alekssandr89/Dixom-m/Dixom_pm/assets/images/jpg/night.jpg

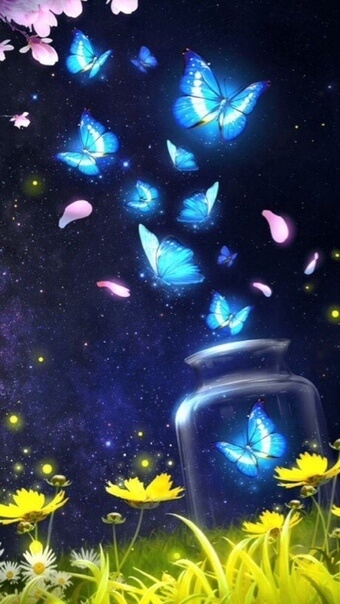
Dixom_pm/assets/images/jpg/night.jpg
