alekssandr89/Dixom-m/Dixom_pm/assets/images/jpg/rotate.jpg

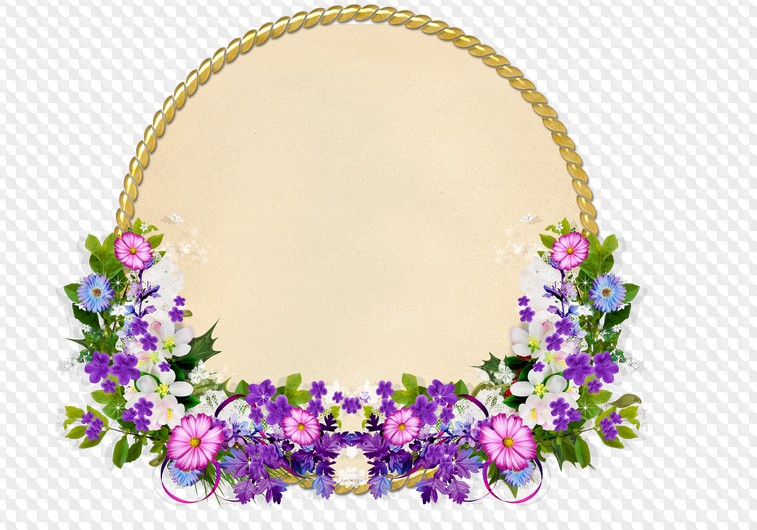
Dixom_pm/assets/images/jpg/rotate.jpg
