alekssandr89/Dixom-m/Dixom_pm/assets/images/png/speaker.png

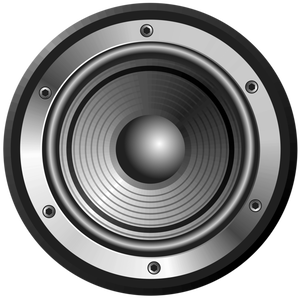
Dixom_pm/assets/images/png/speaker.png
