alekssandr89/Dixom-m/Dixom_pm/assets/texture/noise.jpg

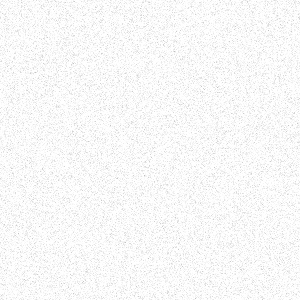
Dixom_pm/assets/texture/noise.jpg
