alekssandr89/Dixom-m/pcb/Base/electrical_diagram.png

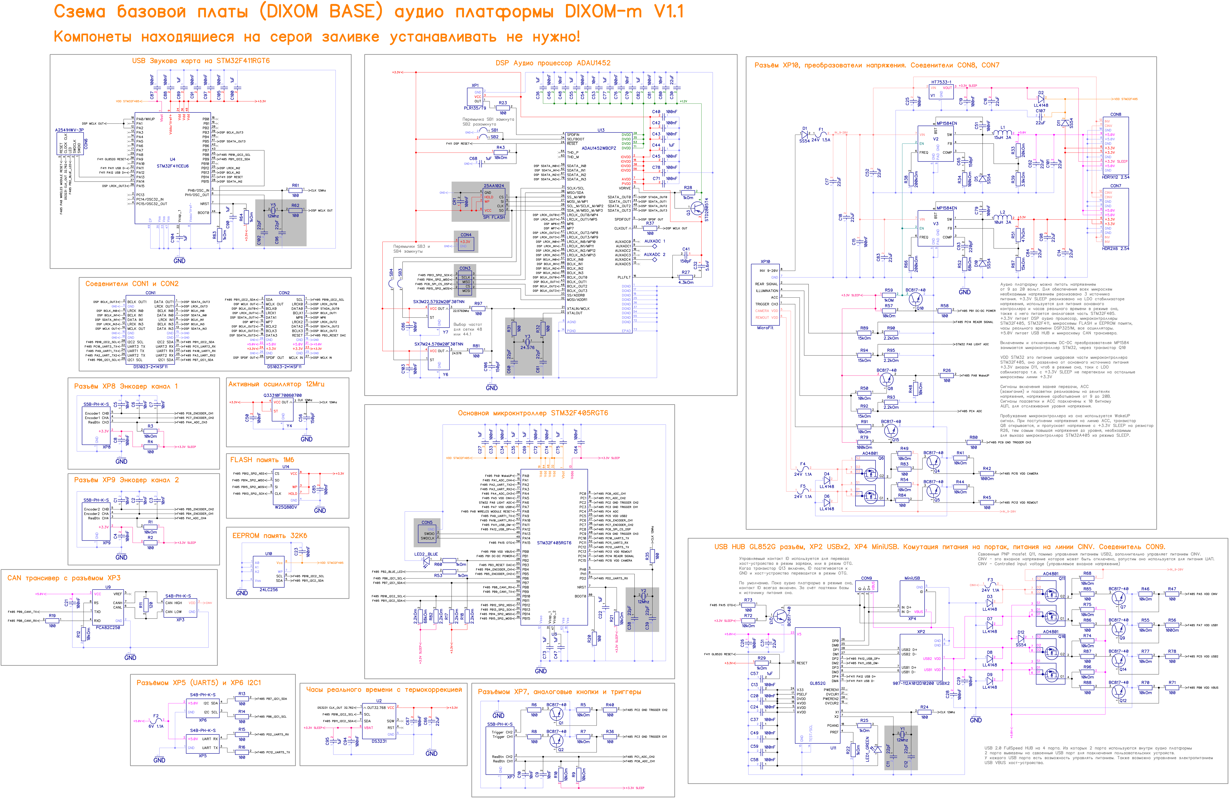
pcb/Base/electrical_diagram.png
