alekssandr89/Dixom-m/pcb/Base/images/1_PCB_TOP.png

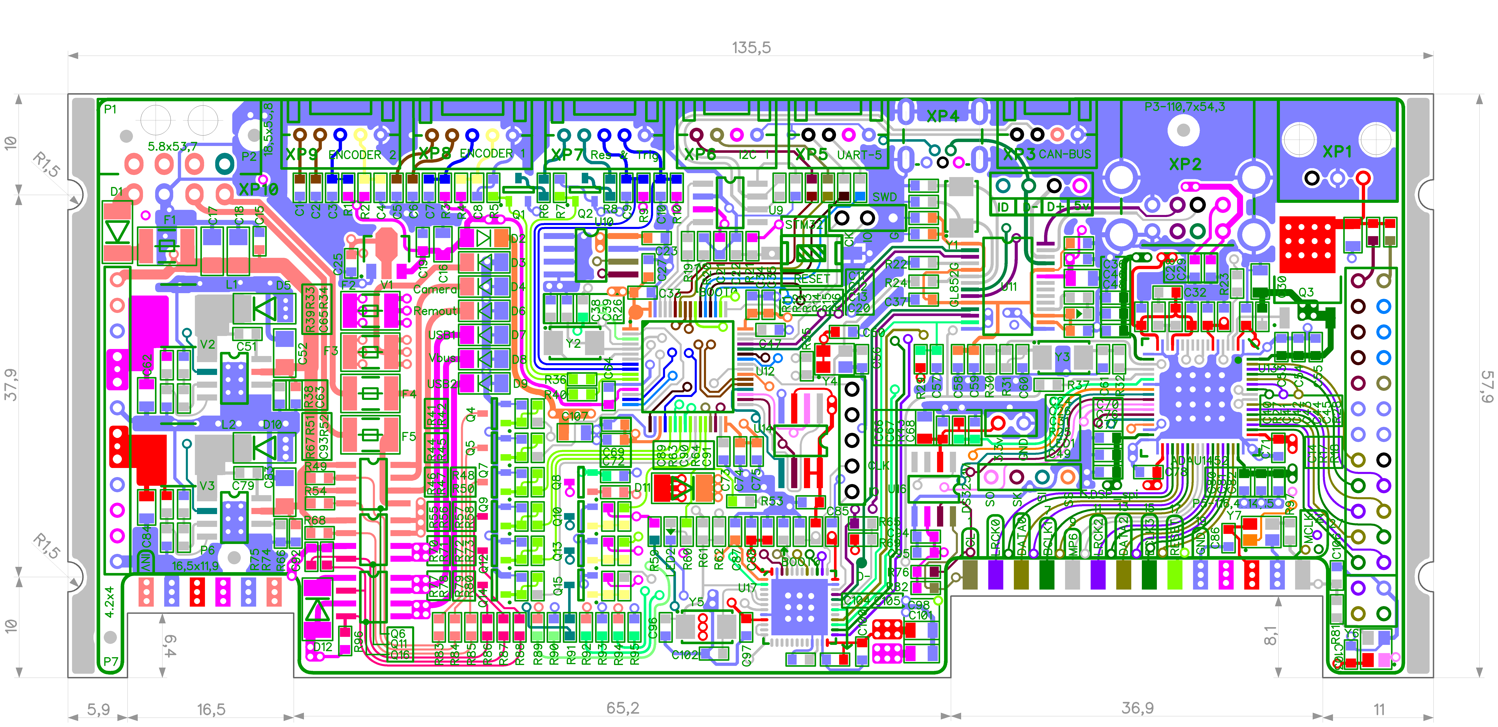
pcb/Base/images/1_PCB_TOP.png
