alekssandr89/Dixom-m/pcb/Base/images/2_PCB_IN1_GND.png

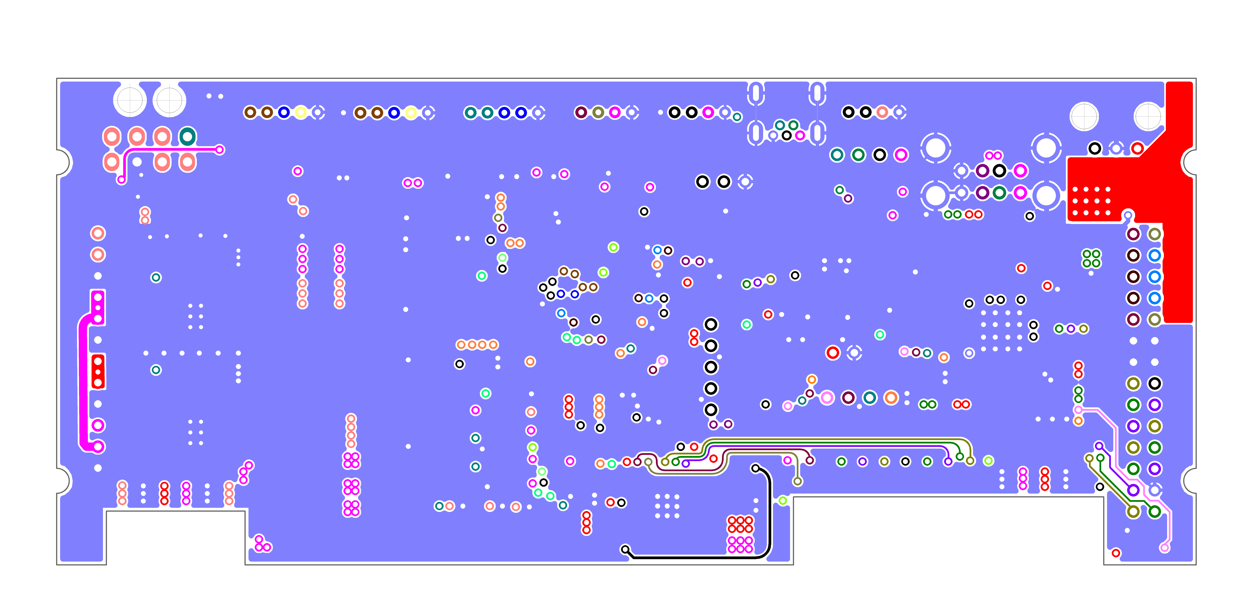
pcb/Base/images/2_PCB_IN1_GND.png
