alekssandr89/Dixom-m/pcb/Base/images/3_PCB_IN2_VCC.png

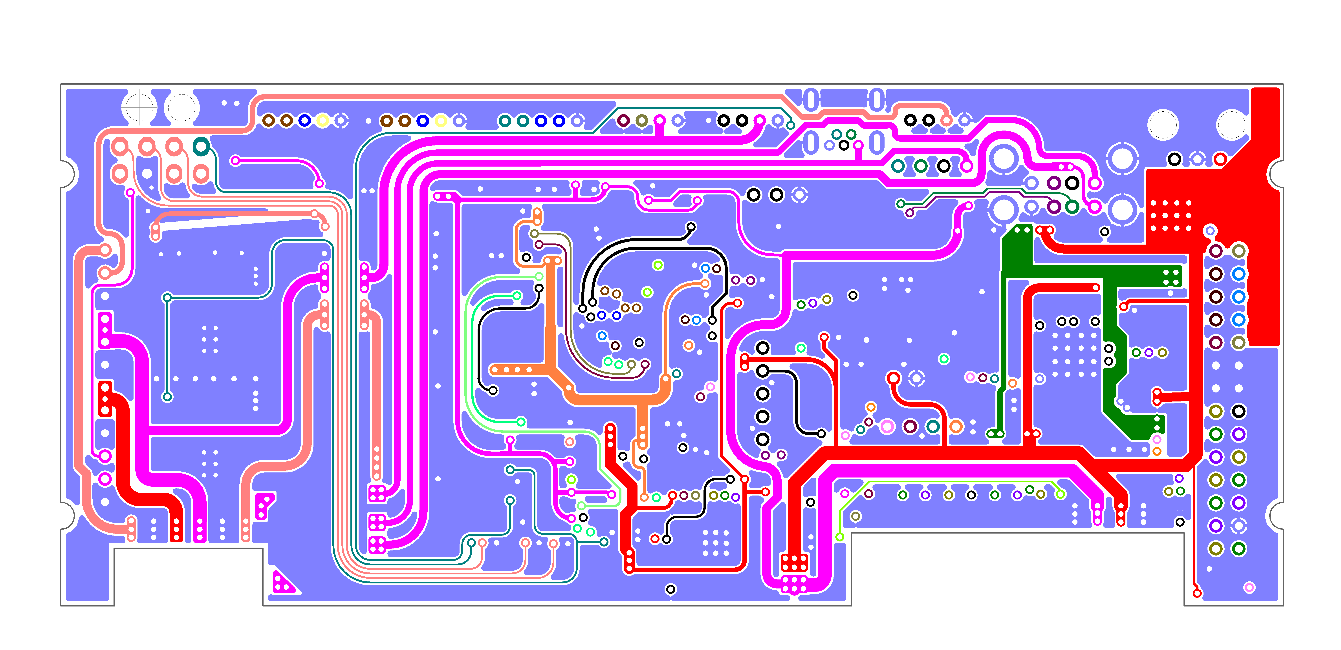
pcb/Base/images/3_PCB_IN2_VCC.png
