alekssandr89/Dixom-m/pcb/Base/images/4_PCB_BOTTOM.png

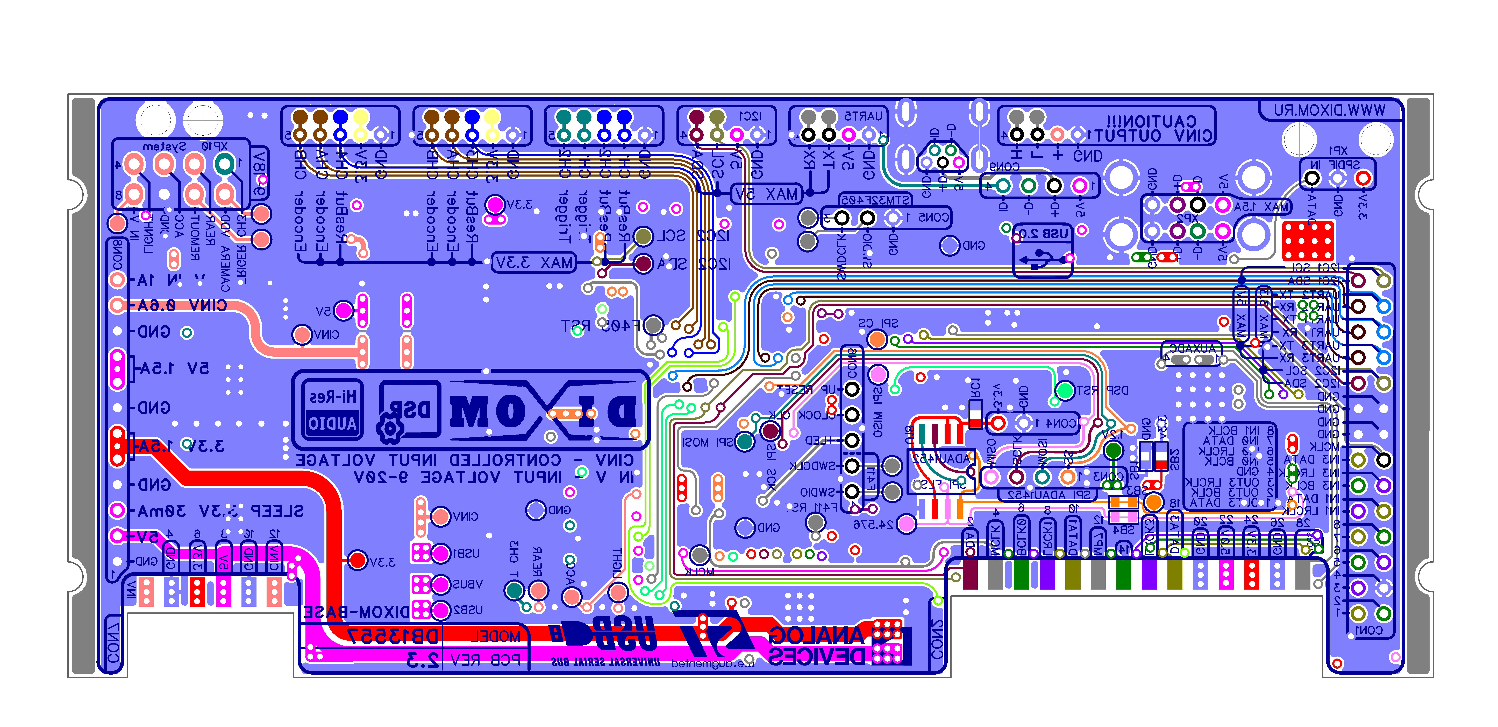
pcb/Base/images/4_PCB_BOTTOM.png
