alekssandr89/Dixom-m/pcb/Base/images/BaseUpdate.jpg

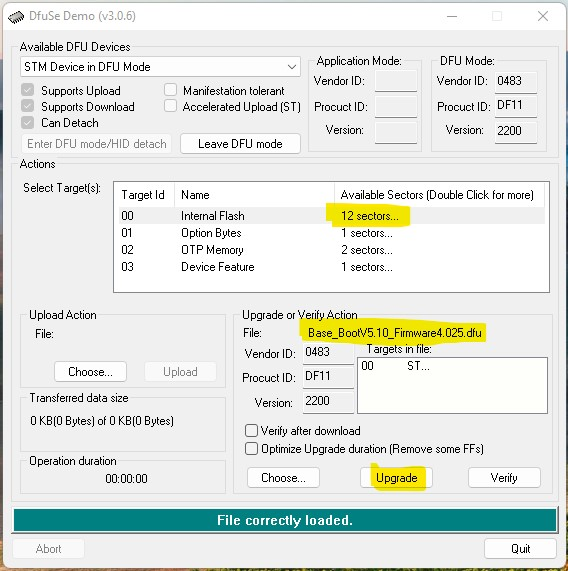
pcb/Base/images/BaseUpdate.jpg
