alekssandr89/Dixom-m/pcb/Base/images/Update.jpg

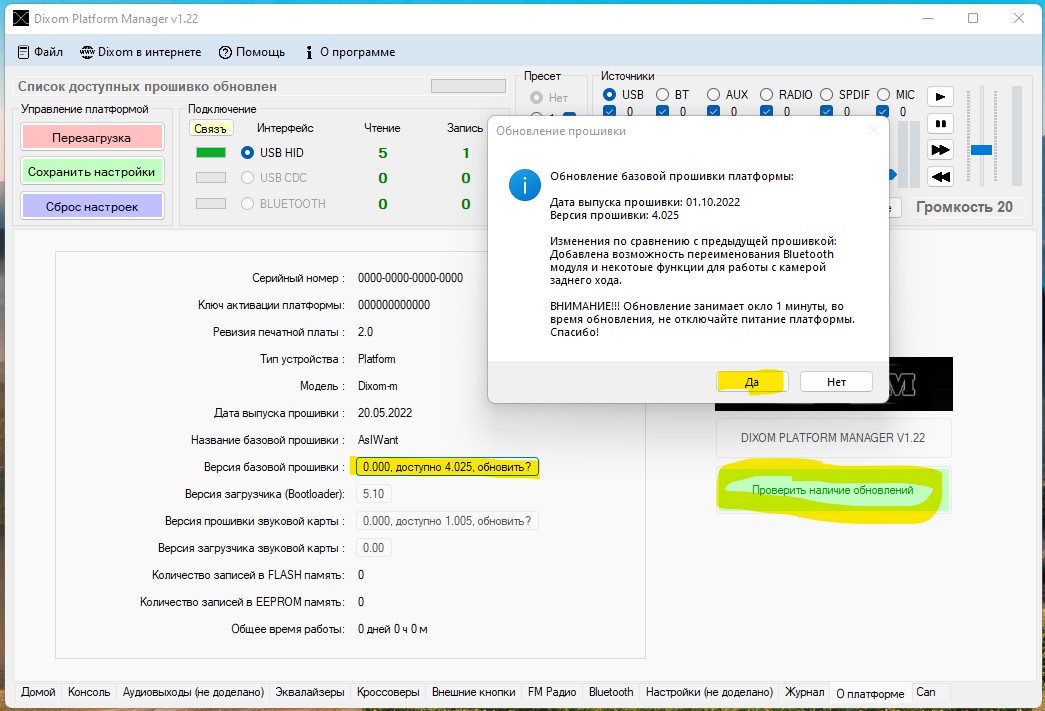
pcb/Base/images/Update.jpg
