alekssandr89/Dixom-m/pcb/Base/images/UpdateDone.jpg

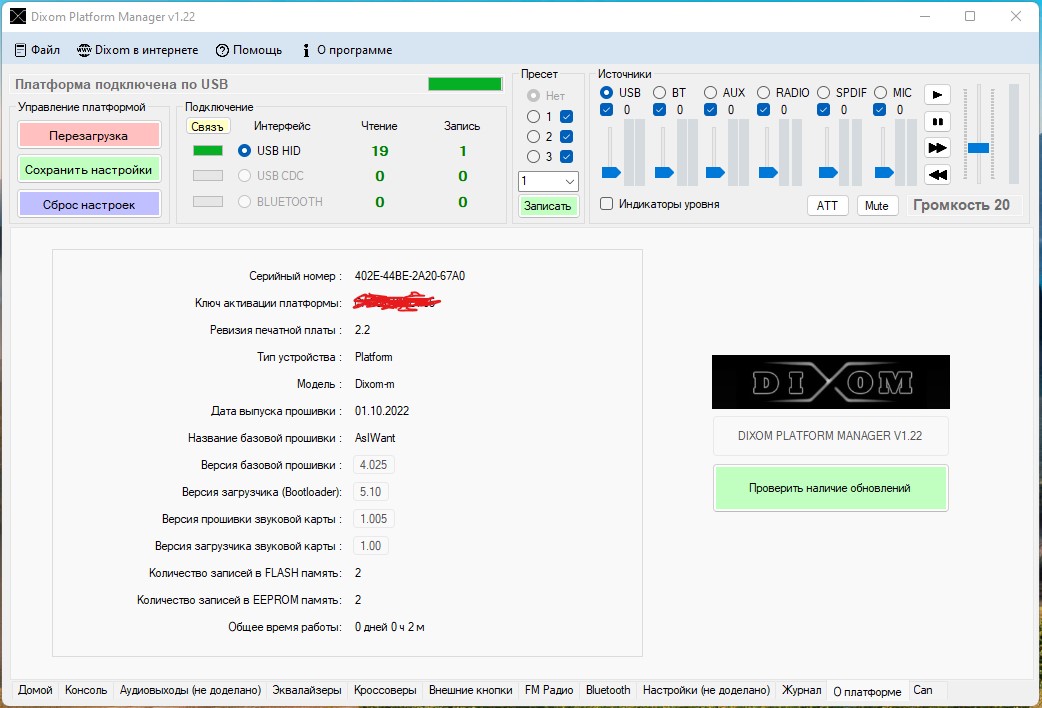
pcb/Base/images/UpdateDone.jpg
