alekssandr89/Dixom-m/Firmware/Dixom_m_Base_Inspiration/Dixom/Pereferiya/GPIO/Inc/Encoder.h

#ifndef __ENCODER_H__
#define __ENCODER_H__

void             ResKeyEnc1(uint16_t AdcVal);
void             ResKeyEnc2(uint16_t AdcVal);
void             ENCODER1(void);
void             ENCODER2(void);
void             ecnDirection1(void);
void             ecnDirection2(void);


#endif
