alekssandr89/Dixom-m/Firmware/Dixom_m_Base_Inspiration/Dixom/Module/DSP/DSP_ElementAddres.h

#ifndef __DSP_ELEMENTADDRES_H_
#define __DSP_ELEMENTADDRES_H_

#include "DSP_Constant.h"
#include "Base_DSP_ADAU1452_PARAM.h"
#include "DIXOM_DAC_ADAU1962_REG.h"
#include <CrystalSix140DThermometer.h>


#define GroupName1        "Tweeters"
#define GroupName2        "Front"
#define GroupName3        "Rear"
#define GroupName4        "Subwoofer"
#define GroupName5        "Group 1"
#define GroupName6        "Group 2"
#define GroupName7        "SPDIF OUT"
#define PresetName        "%hhu Preset"
#define ChannelName1      "%hhu Channel"
#define DelayGroupName    "%hhu Delay group"


static const uint8_t  DEF_POINT_FILTR [20] = {0x00, 0x00, 0x00, 0x00, 0x00, 0x00, 0x00, 0x00, 0x01, 0x00, 0x00, 0x00, 0x00, 0x00, 0x00, 0x00, 0x00, 0x00, 0x00, 0x00 };
static const uint8_t  DEF_VOLUM_ON    [4]  = {0x01, 0x00, 0x00, 0x00 };
static const uint8_t  DEF_VOLUM_OFF   [4]  = {0x00, 0x00, 0x00, 0x01 };


#define DSP_NoiseSwitchAddr        ADDR_NOISE_ENABLENOISE
#define DSP_NoiseGainAddr          ADDR_NOISE_ENABLENOISE
#define DSP_SinGenSwitchAddr       ADDR_SINUS_GAIN_00
#define DSP_SinGenFreqAddr         ADDR_SINUS_INCREMENT

const uint16_t DSP_GENERAL_EQ_ADDR[NUM_ELEM_EQ_GENERAL] = {

ADDR_EQ_USB_ST0_B2,     //0
ADDR_EQ_USB_ST1_B2,     //1
ADDR_EQ_USB_ST2_B2,     //2
ADDR_EQ_USB_ST3_B2,     //3
ADDR_EQ_USB_ST4_B2,     //4

ADDR_EQ_USB_2_ST0_B2,     //5
ADDR_EQ_USB_2_ST1_B2,     //6
ADDR_EQ_USB_2_ST2_B2,     //7
ADDR_EQ_USB_2_ST3_B2,     //8
ADDR_EQ_USB_2_ST4_B2,     //9

ADDR_EQ_USB_3_ST0_B2,    //10
ADDR_EQ_USB_3_ST1_B2,    //11
ADDR_EQ_USB_3_ST2_B2,    //12
ADDR_EQ_USB_3_ST3_B2,    //13
ADDR_EQ_USB_3_ST4_B2,    //14

ADDR_EQ_USB_4_ST0_B2,     //15
ADDR_EQ_USB_4_ST1_B2,     //16
ADDR_EQ_USB_4_ST2_B2,     //17
ADDR_EQ_USB_4_ST3_B2,     //18
ADDR_EQ_USB_4_ST4_B2,     //19

ADDR_EQ_USB_5_ST0_B2,     //20
ADDR_EQ_USB_5_ST1_B2,     //21
ADDR_EQ_USB_5_ST2_B2,     //22
ADDR_EQ_USB_5_ST3_B2,     //23
ADDR_EQ_USB_5_ST4_B2,     //24

ADDR_EQ_USB_6_ST0_B2,    //25
ADDR_EQ_USB_6_ST1_B2,    //26
ADDR_EQ_USB_6_ST2_B2,    //27
ADDR_EQ_USB_6_ST3_B2,    //28
ADDR_EQ_USB_6_ST4_B2     //29
};

/*

const uint8_t  DEFAULT_POINT_FILTR [20] = {0x00, 0x00, 0x00, 0x00, 0x00, 0x00, 0x00, 0x00, 0x01, 0x00, 0x00, 0x00, 0x00, 0x00, 0x00, 0x00, 0x00, 0x00, 0x00, 0x00 };

const uint8_t  DEFAULT_VOLUM_OFF   [4]  = {0x00, 0x00, 0x00, 0x01 };
const uint8_t  DEFAULT_VOLUM_ON    [4]  = {0x01, 0x00, 0x00, 0x00 };


*/
const uint16_t SUPPERBASS_DSP_ADDR[NUM_ELEM_SUPPERBASS*3] = {
/*MOD_USBBASS_ALG0_SUPERBASSALGSTEREOS3001COMPBASE0_ADDR,             //0   SUPPERBASS FREQ LEVEL USB
MOD_USBBASS_ALG0_SUPERBASSALGSTEREOS3001K_ADDR,                     //1   SUPPERBASS GAIN LEVEL USB
MOD_USBBASS_ALG0_SUPERBASSALGSTEREOS3001POSTGAIN_ADDR,              //2   SUPPERBASS INTE LEVEL USB

MOD_BLUETOOTHBASS_ALG0_SUPERBASSALGSTEREOS3002COMPBASE0_ADDR,       //3   SUPPERBASS FREQ BLUETOOTH
MOD_BLUETOOTHBASS_ALG0_SUPERBASSALGSTEREOS3002K_ADDR,               //4   SUPPERBASS GAIN BLUETOOTH
MOD_BLUETOOTHBASS_ALG0_SUPERBASSALGSTEREOS3002POSTGAIN_ADDR,        //5   SUPPERBASS INTE BLUETOOTH

MOD_AUXBASS_ALG0_SUPERBASSALGSTEREOS3003COMPBASE0_ADDR,             //6   SUPPERBASS FREQ AUX
MOD_AUXBASS_ALG0_SUPERBASSALGSTEREOS3003K_ADDR,                     //7   SUPPERBASS GAIN AUX
MOD_AUXBASS_ALG0_SUPERBASSALGSTEREOS3003POSTGAIN_ADDR,              //8   SUPPERBASS INTE AUX

MOD_RADIOBASS_ALG0_SUPERBASSALGSTEREOS3004COMPBASE0_ADDR,           //9   SUPPERBASS FREQ RADIO
MOD_RADIOBASS_ALG0_SUPERBASSALGSTEREOS3004K_ADDR,                   //10  SUPPERBASS GAIN RADIO
MOD_RADIOBASS_ALG0_SUPERBASSALGSTEREOS3004POSTGAIN_ADDR,            //11  SUPPERBASS INTE RADIO

MOD_SPDIFBASS_ALG0_SUPERBASSALGSTEREOS3005COMPBASE0_ADDR,           //12  SUPPERBASS FREQ SPDIF
MOD_SPDIFBASS_ALG0_SUPERBASSALGSTEREOS3005K_ADDR,                   //13  SUPPERBASS GAIN SPDIF
MOD_SPDIFBASS_ALG0_SUPERBASSALGSTEREOS3005POSTGAIN_ADDR,            //14  SUPPERBASS INTE SPDIF

MOD_MICBASS_ALG0_SUPERBASSALGSTEREOS3006COMPBASE0_ADDR,             //15  SUPPERBASS FREQ MIC
MOD_MICBASS_ALG0_SUPERBASSALGSTEREOS3006K_ADDR,                     //16  SUPPERBASS GAIN MIC
MOD_MICBASS_ALG0_SUPERBASSALGSTEREOS3006POSTGAIN_ADDR,              //17  SUPPERBASS INTE MIC*/
};

const uint16_t WIDESTEREO_DSP_ADDR[NUM_ELEM_WIDESTEREO] = {
/*MOD_USBESC_ALG0_ESCALGS3001GAIN_ADDR,                               //0   WIDE STEREO LEVEL USB
MOD_BLUETOOTHESC_ALG0_ESCALGS3002GAIN_ADDR,                         //1   WIDE STEREO LEVEL BLUETOOTH
MOD_AUXESC_ALG0_ESCALGS3003GAIN_ADDR,                               //2   WIDE STEREO LEVEL AUX
MOD_RADIOESC_ALG0_ESCALGS3004GAIN_ADDR,                             //3   WIDE STEREO LEVEL RADIO
MOD_SPDIFESC_ALG0_ESCALGS3005GAIN_ADDR,                             //4   WIDE STEREO LEVEL SPDIF
MOD_MICESC_ALG0_ESCALGS3006GAIN_ADDR,                               //5   WIDE STEREO LEVEL MIC*/
};

const uint16_t PHATSTEREO_DSP_ADDR[NUM_ELEM_PHATSTEREO] = {
ADDR_STEREO_USB_SPREAD_LEVEL,             //0   PHAT STEREO LEVEL USB
ADDR_STEREO_BLUETOOTH_SPREAD_LEVEL,       //1   PHAT STEREO LEVEL BLUETOOTH
ADDR_STEREO_AUX_SPREAD_LEVEL,             //2   PHAT STEREO LEVEL AUX
ADDR_STEREO_RADIO_SPREAD_LEVEL,           //3   PHAT STEREO LEVEL RADIO
ADDR_STEREO_SPDIF_SPREAD_LEVEL,           //4   PHAT STEREO LEVEL SPDIF
ADDR_STEREO_MIC_SPREAD_LEVEL,             //5   PHAT STEREO LEVEL MIC
};

const uint16_t GAIN_DSP_ADDR[NUM_ELEM_GAIN] = {
//ADDR_GAIN_CH1_2_TARGET,                           //0   CENTR
ADDR_GAIN_CH1_2_TARGET,                           //1   CH 1 L
ADDR_GAIN_CH1_2_1_GAIN,                           //2   CH 2 R
ADDR_GAIN_CH3_4_TARGET,                           //3   CH 3 L
ADDR_GAIN_CH3_4_1_GAIN,                           //4   CH 4 R
ADDR_GAIN_CH5_6_TARGET,                           //5   CH 5 L
ADDR_GAIN_CH5_6_1_GAIN,                           //6   CH 6 R
ADDR_GAIN_CH7_8_TARGET,                           //7   CH 7 L
ADDR_GAIN_CH7_8_1_GAIN,                           //8   CH 8 R
ADDR_GAIN_CH9_10_TARGET,                          //9   CH 9 L
ADDR_GAIN_CH9_10_1_GAIN,                          //10  CH 10 R
ADDR_GAIN_CH11_12_TARGET,                         //11  CH 11 L
ADDR_GAIN_CH11_12_1_GAIN,                         //12  CH 12 R
ADDR_GAIN_CH11_13_TARGET,                         //13  SPDIF L
ADDR_GAIN_CH11_13_1_GAIN,                         //14  SPDIF R
};


const uint16_t DELAY_DSP_ADDR[NUM_ELEM_DELAY] = {
ADDR_DELAY_CH1L_DELAYAMT,                                       //1   CH 1 L
ADDR_DELAY_CH2R_DELAYAMT,                                       //2   CH 2 R
ADDR_DELAY_CH3L_DELAYAMT,                                       //3   CH 3 L
ADDR_DELAY_CH4R_DELAYAMT,                                       //4   CH 4 R
ADDR_DELAY_CH5L_DELAYAMT,                                       //5   CH 5 L
ADDR_DELAY_CH6R_DELAYAMT,                                       //6   CH 6 R
ADDR_DELAY_CH7L_DELAYAMT,                                       //7   CH 7 L
ADDR_DELAY_CH8R_DELAYAMT,                                       //8   CH 8 R
ADDR_DELAY_CH9L_DELAYAMT,                                       //9   CH 9 L
ADDR_DELAY_CH10R_DELAYAMT,                                      //10  CH 10 R
ADDR_DELAY_CH11L_DELAYAMT,                                      //11  CH 11 L
ADDR_DELAY_CH12R_DELAYAMT,                                      //12  CH 12 R
ADDR_DELAY_SPDIFL_DELAYAMT,                                     //13  SPDIF L
ADDR_DELAY_SPDIFR_DELAYAMT,                                     //14  SPDIF R
};

const uint16_t LIMITER_DSP_ADDR[NUM_ELEM_LIMITER * 3] = {
///        ADDR THRESHOLD                           ADDR RMS                           ADDR DECAY
/*MOD_LIMITER_CH1L_ALG0_THRESHOLD_ADDR,    MOD_LIMITER_CH1L_ALG0_RMS_ADDR,    MOD_LIMITER_CH1L_ALG0_DECAY_ADDR,    //0   CH 1 L
MOD_LIMITER_CH2R_ALG0_THRESHOLD_ADDR,    MOD_LIMITER_CH2R_ALG0_RMS_ADDR,    MOD_LIMITER_CH2R_ALG0_DECAY_ADDR,    //1   CH 2 R
MOD_LIMITER_CH3L_ALG0_THRESHOLD_ADDR,    MOD_LIMITER_CH3L_ALG0_RMS_ADDR,    MOD_LIMITER_CH3L_ALG0_DECAY_ADDR,    //2   CH 3 L
MOD_LIMITER_CH4R_ALG0_THRESHOLD_ADDR,    MOD_LIMITER_CH4R_ALG0_RMS_ADDR,    MOD_LIMITER_CH4R_ALG0_DECAY_ADDR,    //3   CH 4 R
MOD_LIMITER_CH5L_ALG0_THRESHOLD_ADDR,    MOD_LIMITER_CH5L_ALG0_RMS_ADDR,    MOD_LIMITER_CH5L_ALG0_DECAY_ADDR,    //4   CH 5 L
MOD_LIMITER_CH6R_ALG0_THRESHOLD_ADDR,    MOD_LIMITER_CH6R_ALG0_RMS_ADDR,    MOD_LIMITER_CH6R_ALG0_DECAY_ADDR,    //5   CH 6 R
MOD_LIMITER_CH7L_ALG0_THRESHOLD_ADDR,    MOD_LIMITER_CH7L_ALG0_RMS_ADDR,    MOD_LIMITER_CH7L_ALG0_DECAY_ADDR,    //6   CH 7 L
MOD_LIMITER_CH8R_ALG0_THRESHOLD_ADDR,    MOD_LIMITER_CH8R_ALG0_RMS_ADDR,    MOD_LIMITER_CH8R_ALG0_DECAY_ADDR,    //7   CH 8 R
MOD_LIMITER_CH9L_ALG0_THRESHOLD_ADDR,    MOD_LIMITER_CH9L_ALG0_RMS_ADDR,    MOD_LIMITER_CH9L_ALG0_DECAY_ADDR,    //8   CH 9 L
MOD_LIMITER_CH10R_ALG0_THRESHOLD_ADDR,   MOD_LIMITER_CH10R_ALG0_RMS_ADDR,   MOD_LIMITER_CH10R_ALG0_DECAY_ADDR,   //9   CH 10 R
MOD_LIMITER_CH11L_ALG0_THRESHOLD_ADDR,   MOD_LIMITER_CH11L_ALG0_RMS_ADDR,   MOD_LIMITER_CH11L_ALG0_DECAY_ADDR,   //10  CH 11 R
MOD_LIMITER_CH12R_ALG0_THRESHOLD_ADDR,   MOD_LIMITER_CH12R_ALG0_RMS_ADDR,   MOD_LIMITER_CH12R_ALG0_DECAY_ADDR,   //11  CH 12 R
MOD_LIMITER_CH13L_ALG0_THRESHOLD_ADDR,   MOD_LIMITER_CH13L_ALG0_RMS_ADDR,   MOD_LIMITER_CH13L_ALG0_DECAY_ADDR,   //12  SPDIF L
MOD_LIMITER_CH14R_ALG0_THRESHOLD_ADDR,   MOD_LIMITER_CH14R_ALG0_RMS_ADDR,   MOD_LIMITER_CH14R_ALG0_DECAY_ADDR,   //13  SPDIF R*/
};

const uint16_t LOUDNESS_DSP_ADDR[NUM_ELEM_LOUDNESS] = {
ADDR_LOUDNESS_USB_IIR_COEFF_A1_HI,         //0   LOUDNESSS USB
ADDR_LOUDNESS_BLUETOOTH_IIR_COEFF_A1_HI,   //1   LOUDNESSS BLUETOOTH
ADDR_LOUDNESS_AUX_IIR_COEFF_A1_HI,         //2   LOUDNESSS AUX
ADDR_LOUDNESS_RADIO_IIR_COEFF_A1_HI,       //3   LOUDNESSS RADIO
ADDR_LOUDNESS_SPDIF_IIR_COEFF_A1_HI,       //4   LOUDNESSS SPDIF
ADDR_LOUDNESS_MIC_IIR_COEFF_A1_HI,         //5   LOUDNESSS MIC
};

const uint16_t INVERT_DSP_ADDR[NUM_ELEM_INVERT] = {
ADDR_INVERT_CH1L_INVERT,                            //1    CH 1 L
ADDR_INVERT_CH2R_INVERT,                            //2    CH 2 R
ADDR_INVERT_CH3L_INVERT,                            //3    CH 3 L
ADDR_INVERT_CH4R_INVERT,                            //4    CH 4 R
ADDR_INVERT_CH5L_INVERT,                            //5    CH 5 L
ADDR_INVERT_CH6R_INVERT,                            //6    CH 6 R
ADDR_INVERT_CH7L_INVERT,                            //7    CH 7 L
ADDR_INVERT_CH8R_INVERT,                            //8    CH 8 R
ADDR_INVERT_CH9L_INVERT,                            //9    CH 9 L
ADDR_INVERT_CH10R_INVERT,                          //10   CH 10 R
ADDR_INVERT_CH11L_INVERT,                          //11   CH 11 L
ADDR_INVERT_CH12R_INVERT,                          //12   CH 12 R
ADDR_INVERT_SPDIFL_INVERT,                          //13   CH SPDIF L
ADDR_INVERT_CH14R_INVERT,                          //14   CH SPDIF R
ADDR_INVERT_USB_L_INVERT,                          //15   USB L
ADDR_INVERT_USB_R_INVERT,                          //16   USB R
ADDR_INVERT_BLUETOOTH_L_INVERT,                    //17   BLUETOOTH L
ADDR_INVERT_BLUETOOTH_R_INVERT,                    //18   BLUETOOTH R
ADDR_INVERT_AUX_L_INVERT,                          //19   AUX L
ADDR_INVERT_AUX_R_INVERT,                          //20   AUX R
ADDR_INVERT_RADIO_L_INVERT,                        //21   RADIO L
ADDR_INVERT_RADIO_R_INVERT,                        //22   RADIO R
ADDR_INVERT_SPDIF_L_INVERT,                        //23   SPDIF L
ADDR_INVERT_SPDIF_R_INVERT,                        //24   SPDIF R
ADDR_INVERT_MIC_L_INVERT,                          //25   MIC L
ADDR_INVERT_MIC_R_INVERT,                          //26   MIC R
0
};


const uint16_t VOLUM_DSP_ADDR[NUM_ELEM_VOL] = {
ADDR_VOL_MASTER_GAIN,                                   //0   DAC MASTE VOL
0,                                                                   //1
0,                                                                   //2
0,                                                                   //3
ADDR_VOL_MIC_GAIN,                                //4   MIN VOL MIC
ADDR_VOL_USB_GAIN,                                 //5   MIN VOL USB
ADDR_VOL_BLUETOOTH_GAIN,                           //6   MIN VOL BLUETOOTH
ADDR_VOL_AUX_GAIN,                                 //7   MIN VOL AUX
ADDR_VOL_RADIO_GAIN,                               //8   MIN VOL RADIO
ADDR_VOL_SPDIF_GAIN,                               //9   MIN VOL SPDIF
ADDR_VOL_MASTER_GAIN,                              //10
ADDR_VOL_USB_GAIN,                                 //11  USB_VOL
ADDR_AUDIOROUTER_INPUTGAIN_0,     //12  USB_L
ADDR_AUDIOROUTER_INPUTGAIN_1,     //13  USB_R
ADDR_VOL_BLUETOOTH_GAIN,                           //14  BLUETOOTH_VOL
ADDR_AUDIOROUTER_INPUTGAIN_2,     //15  BLUETOOTH_L
ADDR_AUDIOROUTER_INPUTGAIN_3,     //16  BLUETOOTH_R
ADDR_VOL_AUX_GAIN,                                 //17  AUX_VOL
ADDR_AUDIOROUTER_INPUTGAIN_4,     //18  AUX_L
ADDR_AUDIOROUTER_INPUTGAIN_5,     //19  AUX_R
ADDR_VOL_RADIO_GAIN,                               //20  RADIO_VOL
ADDR_AUDIOROUTER_INPUTGAIN_6,     //21  RADIO_L
ADDR_AUDIOROUTER_INPUTGAIN_7,     //22  RADIO_R
ADDR_VOL_SPDIF_GAIN,                               //23  SPDIF_VOL
ADDR_AUDIOROUTER_INPUTGAIN_8,     //24  SPDIF_L
ADDR_AUDIOROUTER_INPUTGAIN_9,     //25  SPDIF_R
ADDR_VOL_MIC_GAIN,                                //26  MIC
ADDR_AUDIOROUTER_INPUTGAIN_10,    //27  MIC_L
ADDR_AUDIOROUTER_INPUTGAIN_11,    //28  MIC_R
ADDR_OUT_VOL_CH1L_2R_GAIN,                         //29  VOL_OUT_CH1_2LR
ADDR_AUDIOROUTER_OUTPUTGAIN_0,    //30  VOL_OUT_CH1L
ADDR_AUDIOROUTER_OUTPUTGAIN_1,    //31  VOL_OUT_CH2R
ADDR_OUT_VOL_CH3L_4R_GAIN,                         //32  VOL_OUT_CH1_2LR
ADDR_AUDIOROUTER_OUTPUTGAIN_2,    //33  VOL_OUT_CH1L
ADDR_AUDIOROUTER_OUTPUTGAIN_3,    //34  VOL_OUT_CH2R
ADDR_OUT_VOL_CH5L_6R_GAIN,                         //35  VOL_OUT_CH1_2LR
ADDR_AUDIOROUTER_OUTPUTGAIN_4,    //36  VOL_OUT_CH1L
ADDR_AUDIOROUTER_OUTPUTGAIN_5,    //37  VOL_OUT_CH2R
ADDR_OUT_VOL_CH7L_8R_GAIN,                        //38  VOL_OUT_CH1_2LR
ADDR_AUDIOROUTER_OUTPUTGAIN_6,    //39  VOL_OUT_CH1L
ADDR_AUDIOROUTER_OUTPUTGAIN_7,    //40  VOL_OUT_CH2R
ADDR_OUT_VOL_CH9L_10R_GAIN,                       //41  VOL_OUT_CH1_2LR
ADDR_AUDIOROUTER_OUTPUTGAIN_8,    //42  VOL_OUT_CH1L
ADDR_AUDIOROUTER_OUTPUTGAIN_9,    //43  VOL_OUT_CH2R
ADDR_OUT_VOL_CH11L_12R_GAIN,                      //44  VOL_OUT_CH1_2LR
ADDR_AUDIOROUTER_OUTPUTGAIN_10,   //45  VOL_OUT_CH1L
ADDR_AUDIOROUTER_OUTPUTGAIN_11,   //46  VOL_OUT_CH2R
ADDR_OUTVOL_SPDIF_GAIN,                           //47  VOL_OUT_CH1_2LR
ADDR_AUDIOROUTER_OUTPUTGAIN_12,   //48  VOL_OUT_SPDIFL
ADDR_AUDIOROUTER_OUTPUTGAIN_13,   //49  VOL_OUT_SPDIFR

ADDR_AUDIOROUTER_CROSSGAIN_0_0,    //50  VOL_USB_L_OUT_CH1L
ADDR_AUDIOROUTER_CROSSGAIN_1_0,    //51  VOL_USB_L_OUT_CH2R
ADDR_AUDIOROUTER_CROSSGAIN_2_0,    //52  VOL_USB_L_OUT_CH3L
ADDR_AUDIOROUTER_CROSSGAIN_3_0,    //53  VOL_USB_L_OUT_CH4R
ADDR_AUDIOROUTER_CROSSGAIN_4_0,    //54  VOL_USB_L_OUT_CH5L
ADDR_AUDIOROUTER_CROSSGAIN_5_0,    //55  VOL_USB_L_OUT_CH6R
ADDR_AUDIOROUTER_CROSSGAIN_6_0,    //56  VOL_USB_L_OUT_CH7L
ADDR_AUDIOROUTER_CROSSGAIN_7_0,    //57  VOL_USB_L_OUT_CH8R
ADDR_AUDIOROUTER_CROSSGAIN_8_0,    //58  VOL_USB_L_OUT_CH9L
ADDR_AUDIOROUTER_CROSSGAIN_9_0,    //59  VOL_USB_L_OUT_CH10R
ADDR_AUDIOROUTER_CROSSGAIN_10_0,   //60  VOL_USB_L_OUT_CH11L
ADDR_AUDIOROUTER_CROSSGAIN_11_0,   //61  VOL_USB_L_OUT_CH12R
ADDR_AUDIOROUTER_CROSSGAIN_12_0,   //62  VOL_USB_L_OUT_SPDIFL
ADDR_AUDIOROUTER_CROSSGAIN_13_0,   //63  VOL_USB_L_OUT_SPDIFR
ADDR_AUDIOROUTER_CROSSGAIN_0_1,    //64  VOL_USB_R_OUT_CH1L
ADDR_AUDIOROUTER_CROSSGAIN_1_1,    //65  VOL_USB_R_OUT_CH2R
ADDR_AUDIOROUTER_CROSSGAIN_2_1,    //66  VOL_USB_R_OUT_CH3L
ADDR_AUDIOROUTER_CROSSGAIN_3_1,    //67  VOL_USB_R_OUT_CH4R
ADDR_AUDIOROUTER_CROSSGAIN_4_1,    //68  VOL_USB_R_OUT_CH5L
ADDR_AUDIOROUTER_CROSSGAIN_5_1,    //69  VOL_USB_R_OUT_CH6R
ADDR_AUDIOROUTER_CROSSGAIN_6_1,    //70  VOL_USB_R_OUT_CH7L
ADDR_AUDIOROUTER_CROSSGAIN_7_1,    //71  VOL_USB_R_OUT_CH8R
ADDR_AUDIOROUTER_CROSSGAIN_8_1,    //72  VOL_USB_R_OUT_CH9L
ADDR_AUDIOROUTER_CROSSGAIN_9_1,    //73  VOL_USB_R_OUT_CH10R
ADDR_AUDIOROUTER_CROSSGAIN_10_1,   //74  VOL_USB_R_OUT_CH11L
ADDR_AUDIOROUTER_CROSSGAIN_11_1,   //75  VOL_USB_R_OUT_CH12R
ADDR_AUDIOROUTER_CROSSGAIN_12_1,   //76  VOL_USB_R_OUT_SPDIFL
ADDR_AUDIOROUTER_CROSSGAIN_13_1,   //77  VOL_USB_R_OUT_SPDIFR
ADDR_AUDIOROUTER_CROSSGAIN_0_2,    //78  VOL_BLUETOOTH_L_OUT_CH1L
ADDR_AUDIOROUTER_CROSSGAIN_1_2,    //79  VOL_BLUETOOTH_L_OUT_CH2R
ADDR_AUDIOROUTER_CROSSGAIN_2_2,    //80  VOL_BLUETOOTH_L_OUT_CH3L
ADDR_AUDIOROUTER_CROSSGAIN_3_2,    //81  VOL_BLUETOOTH_L_OUT_CH4R
ADDR_AUDIOROUTER_CROSSGAIN_4_2,    //82  VOL_BLUETOOTH_L_OUT_CH5L
ADDR_AUDIOROUTER_CROSSGAIN_5_2,    //83  VOL_BLUETOOTH_L_OUT_CH6R
ADDR_AUDIOROUTER_CROSSGAIN_6_2,    //84  VOL_BLUETOOTH_L_OUT_CH7L
ADDR_AUDIOROUTER_CROSSGAIN_7_2,    //85  VOL_BLUETOOTH_L_OUT_CH8R
ADDR_AUDIOROUTER_CROSSGAIN_8_2,    //86  VOL_BLUETOOTH_L_OUT_CH9L
ADDR_AUDIOROUTER_CROSSGAIN_9_2,    //87  VOL_BLUETOOTH_L_OUT_CH10R
ADDR_AUDIOROUTER_CROSSGAIN_10_2,   //88  VOL_BLUETOOTH_L_OUT_CH11L
ADDR_AUDIOROUTER_CROSSGAIN_11_2,   //89  VOL_BLUETOOTH_L_OUT_CH12R
ADDR_AUDIOROUTER_CROSSGAIN_12_2,   //90  VOL_BLUETOOTH_L_OUT_SPDIFL
ADDR_AUDIOROUTER_CROSSGAIN_13_2,   //91  VOL_BLUETOOTH_L_OUT_SPDIFR
ADDR_AUDIOROUTER_CROSSGAIN_0_3,    //92  VOL_BLUETOOTH_R_OUT_CH1L
ADDR_AUDIOROUTER_CROSSGAIN_1_3,    //93  VOL_BLUETOOTH_R_OUT_CH2R
ADDR_AUDIOROUTER_CROSSGAIN_2_3,    //94  VOL_BLUETOOTH_R_OUT_CH3L
ADDR_AUDIOROUTER_CROSSGAIN_3_3,    //95  VOL_BLUETOOTH_R_OUT_CH4R
ADDR_AUDIOROUTER_CROSSGAIN_4_3,    //96  VOL_BLUETOOTH_R_OUT_CH5L
ADDR_AUDIOROUTER_CROSSGAIN_5_3,    //97  VOL_BLUETOOTH_R_OUT_CH6R
ADDR_AUDIOROUTER_CROSSGAIN_6_3,    //98  VOL_BLUETOOTH_R_OUT_CH7L
ADDR_AUDIOROUTER_CROSSGAIN_7_3,    //99  VOL_BLUETOOTH_R_OUT_CH8R
ADDR_AUDIOROUTER_CROSSGAIN_8_3,    //100 VOL_BLUETOOTH_R_OUT_CH9L
ADDR_AUDIOROUTER_CROSSGAIN_9_3,    //101 VOL_BLUETOOTH_R_OUT_CH10R
ADDR_AUDIOROUTER_CROSSGAIN_10_3,   //102 VOL_BLUETOOTH_R_OUT_CH11L
ADDR_AUDIOROUTER_CROSSGAIN_11_3,   //103 VOL_BLUETOOTH_R_OUT_CH12R
ADDR_AUDIOROUTER_CROSSGAIN_12_3,   //104 VOL_BLUETOOTH_R_OUT_SPDIFL
ADDR_AUDIOROUTER_CROSSGAIN_13_3,   //105 VOL_BLUETOOTH_R_OUT_SPDIFR
ADDR_AUDIOROUTER_CROSSGAIN_0_4,    //106 VOL_AUX_L_OUT_CH1L
ADDR_AUDIOROUTER_CROSSGAIN_1_4,    //107 VOL_AUX_L_OUT_CH2R
ADDR_AUDIOROUTER_CROSSGAIN_2_4,    //108 VOL_AUX_L_OUT_CH3L
ADDR_AUDIOROUTER_CROSSGAIN_3_4,    //109 VOL_AUX_L_OUT_CH4R
ADDR_AUDIOROUTER_CROSSGAIN_4_4,    //110 VOL_AUX_L_OUT_CH5L
ADDR_AUDIOROUTER_CROSSGAIN_5_4,    //111 VOL_AUX_L_OUT_CH6R
ADDR_AUDIOROUTER_CROSSGAIN_6_4,    //112 VOL_AUX_L_OUT_CH7L
ADDR_AUDIOROUTER_CROSSGAIN_7_4,    //113 VOL_AUX_L_OUT_CH8R
ADDR_AUDIOROUTER_CROSSGAIN_8_4,    //114 VOL_AUX_L_OUT_CH9L
ADDR_AUDIOROUTER_CROSSGAIN_9_4,    //115 VOL_AUX_L_OUT_CH10R
ADDR_AUDIOROUTER_CROSSGAIN_10_4,   //116 VOL_AUX_L_OUT_CH11L
ADDR_AUDIOROUTER_CROSSGAIN_11_4,   //117 VOL_AUX_L_OUT_CH12R
ADDR_AUDIOROUTER_CROSSGAIN_12_4,   //118 VOL_AUX_L_OUT_SPDIFL
ADDR_AUDIOROUTER_CROSSGAIN_13_4,   //119 VOL_AUX_L_OUT_SPDIFR
ADDR_AUDIOROUTER_CROSSGAIN_0_5,    //120 VOL_AUX_R_OUT_CH1L
ADDR_AUDIOROUTER_CROSSGAIN_1_5,    //121 VOL_AUX_R_OUT_CH2R
ADDR_AUDIOROUTER_CROSSGAIN_2_5,    //122 VOL_AUX_R_OUT_CH3L
ADDR_AUDIOROUTER_CROSSGAIN_3_5,    //123 VOL_AUX_R_OUT_CH4R
ADDR_AUDIOROUTER_CROSSGAIN_4_5,    //124 VOL_AUX_R_OUT_CH5L
ADDR_AUDIOROUTER_CROSSGAIN_5_5,    //125 VOL_AUX_R_OUT_CH6R
ADDR_AUDIOROUTER_CROSSGAIN_6_5,    //126 VOL_AUX_R_OUT_CH7L
ADDR_AUDIOROUTER_CROSSGAIN_7_5,    //127 VOL_AUX_R_OUT_CH8R
ADDR_AUDIOROUTER_CROSSGAIN_8_5,    //128 VOL_AUX_R_OUT_CH9L
ADDR_AUDIOROUTER_CROSSGAIN_9_5,    //129 VOL_AUX_R_OUT_CH10R
ADDR_AUDIOROUTER_CROSSGAIN_10_5,   //130 VOL_AUX_R_OUT_CH11L
ADDR_AUDIOROUTER_CROSSGAIN_11_5,   //131 VOL_AUX_R_OUT_CH12R
ADDR_AUDIOROUTER_CROSSGAIN_12_5,   //132 VOL_AUX_R_OUT_SPDIFL
ADDR_AUDIOROUTER_CROSSGAIN_13_5,   //133 VOL_AUX_R_OUT_SPDIFR
ADDR_AUDIOROUTER_CROSSGAIN_0_6,    //134 VOL_RADIO_L_OUT_CH1L
ADDR_AUDIOROUTER_CROSSGAIN_1_6,    //135 VOL_RADIO_L_OUT_CH2R
ADDR_AUDIOROUTER_CROSSGAIN_2_6,    //136 VOL_RADIO_L_OUT_CH3L
ADDR_AUDIOROUTER_CROSSGAIN_3_6,    //137 VOL_RADIO_L_OUT_CH4R
ADDR_AUDIOROUTER_CROSSGAIN_4_6,    //138 VOL_RADIO_L_OUT_CH5L
ADDR_AUDIOROUTER_CROSSGAIN_5_6,    //139 VOL_RADIO_L_OUT_CH6R
ADDR_AUDIOROUTER_CROSSGAIN_6_6,    //140 VOL_RADIO_L_OUT_CH7L
ADDR_AUDIOROUTER_CROSSGAIN_7_6,    //141 VOL_RADIO_L_OUT_CH8R
ADDR_AUDIOROUTER_CROSSGAIN_8_6,    //142 VOL_RADIO_L_OUT_CH9L
ADDR_AUDIOROUTER_CROSSGAIN_9_6,    //143 VOL_RADIO_L_OUT_CH10R
ADDR_AUDIOROUTER_CROSSGAIN_10_6,   //144 VOL_RADIO_L_OUT_CH11L
ADDR_AUDIOROUTER_CROSSGAIN_11_6,   //145 VOL_RADIO_L_OUT_CH12R
ADDR_AUDIOROUTER_CROSSGAIN_12_6,   //146 VOL_RADIO_L_OUT_SPDIFL
ADDR_AUDIOROUTER_CROSSGAIN_13_6,   //147 VOL_RADIO_L_OUT_SPDIFR
ADDR_AUDIOROUTER_CROSSGAIN_0_7,    //148 VOL_RADIO_R_OUT_CH1L
ADDR_AUDIOROUTER_CROSSGAIN_1_7,    //149 VOL_RADIO_R_OUT_CH2R
ADDR_AUDIOROUTER_CROSSGAIN_2_7,    //150 VOL_RADIO_R_OUT_CH3L
ADDR_AUDIOROUTER_CROSSGAIN_3_7,    //151 VOL_RADIO_R_OUT_CH4R
ADDR_AUDIOROUTER_CROSSGAIN_4_7,    //152 VOL_RADIO_R_OUT_CH5L
ADDR_AUDIOROUTER_CROSSGAIN_5_7,    //153 VOL_RADIO_R_OUT_CH6R
ADDR_AUDIOROUTER_CROSSGAIN_6_7,    //154 VOL_RADIO_R_OUT_CH7L
ADDR_AUDIOROUTER_CROSSGAIN_7_7,    //155 VOL_RADIO_R_OUT_CH8R
ADDR_AUDIOROUTER_CROSSGAIN_8_7,    //156 VOL_RADIO_R_OUT_CH9L
ADDR_AUDIOROUTER_CROSSGAIN_9_7,    //157 VOL_RADIO_R_OUT_CH10R
ADDR_AUDIOROUTER_CROSSGAIN_10_7,   //158 VOL_RADIO_R_OUT_CH11L
ADDR_AUDIOROUTER_CROSSGAIN_11_7,   //159 VOL_RADIO_R_OUT_CH12R
ADDR_AUDIOROUTER_CROSSGAIN_12_7,   //160 VOL_RADIO_R_OUT_SPDIFL
ADDR_AUDIOROUTER_CROSSGAIN_13_7,   //161 VOL_RADIO_R_OUT_SPDIFR
ADDR_AUDIOROUTER_CROSSGAIN_0_8,    //162 VOL_SPDIF_L_OUT_CH1L
ADDR_AUDIOROUTER_CROSSGAIN_1_8,    //163 VOL_SPDIF_L_OUT_CH2R
ADDR_AUDIOROUTER_CROSSGAIN_2_8,    //164 VOL_SPDIF_L_OUT_CH3L
ADDR_AUDIOROUTER_CROSSGAIN_3_8,    //165 VOL_SPDIF_L_OUT_CH4R
ADDR_AUDIOROUTER_CROSSGAIN_4_8,    //166 VOL_SPDIF_L_OUT_CH5L
ADDR_AUDIOROUTER_CROSSGAIN_5_8,    //167 VOL_SPDIF_L_OUT_CH6R
ADDR_AUDIOROUTER_CROSSGAIN_6_8,    //168 VOL_SPDIF_L_OUT_CH7L
ADDR_AUDIOROUTER_CROSSGAIN_7_8,    //169 VOL_SPDIF_L_OUT_CH8R
ADDR_AUDIOROUTER_CROSSGAIN_8_8,    //170 VOL_SPDIF_L_OUT_CH9L
ADDR_AUDIOROUTER_CROSSGAIN_9_8,    //171 VOL_SPDIF_L_OUT_CH10R
ADDR_AUDIOROUTER_CROSSGAIN_10_8,   //172 VOL_SPDIF_L_OUT_CH11L
ADDR_AUDIOROUTER_CROSSGAIN_11_8,   //173 VOL_SPDIF_L_OUT_CH12R
ADDR_AUDIOROUTER_CROSSGAIN_12_8,   //174 VOL_SPDIF_L_OUT_SPDIFL
ADDR_AUDIOROUTER_CROSSGAIN_13_8,   //175 VOL_SPDIF_L_OUT_SPDIFR
ADDR_AUDIOROUTER_CROSSGAIN_0_9,    //176 VOL_SPDIF_R_OUT_CH1L
ADDR_AUDIOROUTER_CROSSGAIN_1_9,    //177 VOL_SPDIF_R_OUT_CH2R
ADDR_AUDIOROUTER_CROSSGAIN_2_9,    //178 VOL_SPDIF_R_OUT_CH3L
ADDR_AUDIOROUTER_CROSSGAIN_3_9,    //179 VOL_SPDIF_R_OUT_CH4R
ADDR_AUDIOROUTER_CROSSGAIN_4_9,    //180 VOL_SPDIF_R_OUT_CH5L
ADDR_AUDIOROUTER_CROSSGAIN_5_9,    //181 VOL_SPDIF_R_OUT_CH6R
ADDR_AUDIOROUTER_CROSSGAIN_6_9,    //182 VOL_SPDIF_R_OUT_CH7L
ADDR_AUDIOROUTER_CROSSGAIN_7_9,    //183 VOL_SPDIF_R_OUT_CH8R
ADDR_AUDIOROUTER_CROSSGAIN_8_9,    //184 VOL_SPDIF_R_OUT_CH9L
ADDR_AUDIOROUTER_CROSSGAIN_9_9,    //185 VOL_SPDIF_R_OUT_CH10R
ADDR_AUDIOROUTER_CROSSGAIN_10_9,   //186 VOL_SPDIF_R_OUT_CH11L
ADDR_AUDIOROUTER_CROSSGAIN_11_9,   //187 VOL_SPDIF_R_OUT_CH12R
ADDR_AUDIOROUTER_CROSSGAIN_12_9,   //188 VOL_SPDIF_R_OUT_SPDIFL
ADDR_AUDIOROUTER_CROSSGAIN_13_9,   //189 VOL_SPDIF_R_OUT_SPDIFR
ADDR_AUDIOROUTER_CROSSGAIN_0_10,    //190 VOL_MIC_L_OUT_CH1L
ADDR_AUDIOROUTER_CROSSGAIN_1_10,    //191 VOL_MIC_L_OUT_CH2R
ADDR_AUDIOROUTER_CROSSGAIN_2_10,    //192 VOL_MIC_L_OUT_CH3L
ADDR_AUDIOROUTER_CROSSGAIN_3_10,    //193 VOL_MIC_L_OUT_CH4R
ADDR_AUDIOROUTER_CROSSGAIN_4_10,    //194 VOL_MIC_L_OUT_CH5L
ADDR_AUDIOROUTER_CROSSGAIN_5_10,    //195 VOL_MIC_L_OUT_CH6R
ADDR_AUDIOROUTER_CROSSGAIN_6_10,    //196 VOL_MIC_L_OUT_CH7L
ADDR_AUDIOROUTER_CROSSGAIN_7_10,    //197 VOL_MIC_L_OUT_CH8R
ADDR_AUDIOROUTER_CROSSGAIN_8_10,    //198 VOL_MIC_L_OUT_CH9L
ADDR_AUDIOROUTER_CROSSGAIN_9_10,    //199 VOL_MIC_L_OUT_CH10R
ADDR_AUDIOROUTER_CROSSGAIN_10_10,   //200 VOL_MIC_L_OUT_CH11L
ADDR_AUDIOROUTER_CROSSGAIN_11_10,   //201 VOL_MIC_L_OUT_CH12R
ADDR_AUDIOROUTER_CROSSGAIN_12_10,   //202 VOL_MIC_L_OUT_SPDIFL
ADDR_AUDIOROUTER_CROSSGAIN_13_10,   //203 VOL_MIC_L_OUT_SPDIFR
ADDR_AUDIOROUTER_CROSSGAIN_0_11,    //204 VOL_MIC_R_OUT_CH1L
ADDR_AUDIOROUTER_CROSSGAIN_1_11,    //205 VOL_MIC_R_OUT_CH2R
ADDR_AUDIOROUTER_CROSSGAIN_2_11,    //206 VOL_MIC_R_OUT_CH3L
ADDR_AUDIOROUTER_CROSSGAIN_3_11,    //207 VOL_MIC_R_OUT_CH4R
ADDR_AUDIOROUTER_CROSSGAIN_4_11,    //208 VOL_MIC_R_OUT_CH5L
ADDR_AUDIOROUTER_CROSSGAIN_5_11,    //209 VOL_MIC_R_OUT_CH6R
ADDR_AUDIOROUTER_CROSSGAIN_6_11,    //210 VOL_MIC_R_OUT_CH7L
ADDR_AUDIOROUTER_CROSSGAIN_7_11,    //211 VOL_MIC_R_OUT_CH8R
ADDR_AUDIOROUTER_CROSSGAIN_8_11,    //212 VOL_MIC_R_OUT_CH9L
ADDR_AUDIOROUTER_CROSSGAIN_9_11,    //213 VOL_MIC_R_OUT_CH10R
ADDR_AUDIOROUTER_CROSSGAIN_10_11,   //214 VOL_MIC_R_OUT_CH11L
ADDR_AUDIOROUTER_CROSSGAIN_11_11,   //215 VOL_MIC_R_OUT_CH12R
ADDR_AUDIOROUTER_CROSSGAIN_12_11,   //216 VOL_MIC_R_OUT_SPDIFL
ADDR_AUDIOROUTER_CROSSGAIN_13_11,   //217 VOL_MIC_R_OUT_SPDIFR
ADDR_AUDIOROUTER_INPUTGAIN_12,      //218 VOL_BEEP
ADDR_AUDIOROUTER_CROSSGAIN_0_12,    //219 VOL_BEEP_OUT_CH1L
ADDR_AUDIOROUTER_CROSSGAIN_1_12,    //220 VOL_BEEP_OUT_CH2R
ADDR_AUDIOROUTER_CROSSGAIN_2_12,    //221 VOL_BEEP_OUT_CH3L
ADDR_AUDIOROUTER_CROSSGAIN_3_12,    //222 VOL_BEEP_OUT_CH4R
ADDR_AUDIOROUTER_CROSSGAIN_4_12,    //223 VOL_BEEP_OUT_CH5L
ADDR_AUDIOROUTER_CROSSGAIN_5_12,    //224 VOL_BEEP_OUT_CH6R
ADDR_AUDIOROUTER_CROSSGAIN_6_12,    //225 VOL_BEEP_OUT_CH7L
ADDR_AUDIOROUTER_CROSSGAIN_7_12,    //226 VOL_BEEP_OUT_CH8R
ADDR_AUDIOROUTER_CROSSGAIN_8_12,    //227 VOL_BEEP_OUT_CH9L
ADDR_AUDIOROUTER_CROSSGAIN_9_12,    //228 VOL_BEEP_OUT_CH10R
ADDR_AUDIOROUTER_CROSSGAIN_10_12,   //229 VOL_BEEP_OUT_CH11L
ADDR_AUDIOROUTER_CROSSGAIN_11_12,   //230 VOL_BEEP_OUT_CH12R
ADDR_AUDIOROUTER_CROSSGAIN_12_12,   //231 VOL_BEEP_OUT_SPDIFL
ADDR_AUDIOROUTER_CROSSGAIN_13_12,   //232 VOL_BEEP_OUT_SPDIFR

ADDR_AUDIOROUTER_INPUTGAIN_13,     //233 VOL_NOISE
ADDR_AUDIOROUTER_CROSSGAIN_0_13,    //234 VOL_NOISE_OUT_CH1L
ADDR_AUDIOROUTER_CROSSGAIN_1_13,    //235 VOL_NOISE_OUT_CH2R
ADDR_AUDIOROUTER_CROSSGAIN_2_13,    //236 VOL_NOISE_OUT_CH3L
ADDR_AUDIOROUTER_CROSSGAIN_3_13,    //237 VOL_NOISE_OUT_CH4R
ADDR_AUDIOROUTER_CROSSGAIN_4_13,    //238 VOL_NOISE_OUT_CH5L
ADDR_AUDIOROUTER_CROSSGAIN_5_13,    //239 VOL_NOISE_OUT_CH6R
ADDR_AUDIOROUTER_CROSSGAIN_6_13,    //240 VOL_NOISE_OUT_CH7L
ADDR_AUDIOROUTER_CROSSGAIN_7_13,    //241 VOL_NOISE_OUT_CH8R
ADDR_AUDIOROUTER_CROSSGAIN_8_13,    //242 VOL_NOISE_OUT_CH9L
ADDR_AUDIOROUTER_CROSSGAIN_9_13,    //243 VOL_NOISE_OUT_CH10R
ADDR_AUDIOROUTER_CROSSGAIN_10_13,   //244 VOL_NOISE_OUT_CH11L
ADDR_AUDIOROUTER_CROSSGAIN_11_13,   //245 VOL_NOISE_OUT_CH12R
ADDR_AUDIOROUTER_CROSSGAIN_12_13,   //246 VOL_NOISE_OUT_SPDIFL
ADDR_AUDIOROUTER_CROSSGAIN_13_13    //247 VOL_NOISE_OUT_SPDIFR


};/*

#define  VOL_USB               11
#define  VOL_USB_L             12
#define  VOL_USB_R             13
#define  VOL_BLUETOOTH         14
#define  VOL_BLUETOOTH_L       15
#define  VOL_BLUETOOTH_R       16
#define  VOL_AUX               17
#define  VOL_AUX_L             18
#define  VOL_AUX_R             19
#define  VOL_RADIO             20
#define  VOL_RADIO_L           21
#define  VOL_RADIO_R           22
#define  VOL_SPDIF             23
#define  VOL_SPDIF_L           24
#define  VOL_SPDIF_R           25
#define  VOL_MIC               26
#define  VOL_MIC_L             27
#define  VOL_MIC_R             28
#define  VOL_OUT_CH1_2LR       29
#define  VOL_OUT_CH1L          30
#define  VOL_OUT_CH2R          31
#define  VOL_OUT_CH3_4LR       32
#define  VOL_OUT_CH3L          33
#define  VOL_OUT_CH4R          34
#define  VOL_OUT_CH5_6LR       35
#define  VOL_OUT_CH5L          36
#define  VOL_OUT_CH6R          37
#define  VOL_OUT_CH7_8LR       38
#define  VOL_OUT_CH7L          39
#define  VOL_OUT_CH8R          40
#define  VOL_OUT_CH9_10LR      41
#define  VOL_OUT_CH9L          42
#define  VOL_OUT_CH10R         43
#define  VOL_OUT_CH11_12LR     44
#define  VOL_OUT_CH11L         45
#define  VOL_OUT_CH12R         46
#define  VOL_OUT_SPDIFLR       47
#define  VOL_OUT_SPDIFL        48
#define  VOL_OUT_SPDIFR        49
*/

static const uint16_t DSP_VOL_DEFAULT [NUM_ELEM_VOL] = {

20,         //0    VOL GENERAL MASTER
VOL_MIN,    //1    VOL MAX BLUETOOTH
VOL_MIN,    //2    VOL MAX AUX
VOL_MIN,    //3    VOL MAX RADIO
VOL_MIN,    //4    VOL MAX SPDIF
VOL_MIN,    //5    VOL MIN USB
VOL_MIN,    //6    VOL MIN BLUETOOTH
VOL_MIN,    //7    VOL MIN AUX
VOL_MIN,    //8    VOL MIN RADIO
VOL_MIN,    //9    VOL MIN SPDIF
VOL_MAX,    //10   VOL_MASTER DSP
VOL_MAX,    //11   VOL_USB
VOL_MAX,    //12   VOL_USB_L
VOL_MAX,    //13   VOL_USB_R
VOL_MIN,    //14   VOL_BLUETOOTH
VOL_MAX,    //15   VOL_BLUETOOTH_L
VOL_MAX,    //16   VOL_BLUETOOTH_R
VOL_MIN,    //17   VOL_AUX
VOL_MAX,    //18   VOL_AUX_L
VOL_MAX,    //19   VOL_AUX_R
VOL_MIN,    //20   VOL_RADIO
VOL_MAX,    //21   VOL_RADIO_L
VOL_MAX,    //22   VOL_RADIO_R
VOL_MIN,    //23   VOL_SPDIF
VOL_MAX,    //24   VOL_SPDIF_L
VOL_MAX,    //25   VOL_SPDIF_R
VOL_MIN,    //26   VOL_MIC
VOL_MAX,    //27   VOL_MIC_L
VOL_MAX,    //28   VOL_MIC_R
VOL_MAX,    //29   VOL_OUT_CH1_2LR
VOL_MAX,    //30   VOL_OUT_CH1L
VOL_MAX,    //31   VOL_OUT_CH2R
VOL_MAX,    //32   VOL_OUT_CH3_4LR
VOL_MAX,    //33   VOL_OUT_CH3L
VOL_MAX,    //34   VOL_OUT_CH4R
VOL_MAX,    //35   VOL_OUT_CH5_6LR
VOL_MAX,    //36   VOL_OUT_CH5L
VOL_MAX,    //37   VOL_OUT_CH6R
VOL_MAX,    //38   VOL_OUT_CH7_8LR
VOL_MAX,    //39   VOL_OUT_CH7L
VOL_MAX,    //40   VOL_OUT_CH8R
VOL_MAX,    //41   VOL_OUT_CH9_10LR
VOL_MAX,    //42   VOL_OUT_CH9L
VOL_MAX,    //43   VOL_OUT_CH10R
VOL_MAX,    //44   VOL_OUT_CH11_12LR
VOL_MAX,    //45   VOL_OUT_CH11L
VOL_MAX,    //46   VOL_OUT_CH12R
VOL_MAX,    //47   VOL_OUT_SPDIFLR
VOL_MAX,    //48   VOL_OUT_SPDIFL
VOL_MAX,    //49   VOL_OUT_SPDIFR
VOL_MAX,    //50   VOL_USB_L_OUT_CH1L
VOL_MIN,    //51   VOL_USB_L_OUT_CH2R
VOL_MAX,    //52   VOL_USB_L_OUT_CH3L
VOL_MIN,    //53   VOL_USB_L_OUT_CH4R
VOL_MAX,    //54   VOL_USB_L_OUT_CH5L
VOL_MIN,    //55   VOL_USB_L_OUT_CH6R
VOL_MAX,    //56   VOL_USB_L_OUT_CH7L
VOL_MIN,    //57   VOL_USB_L_OUT_CH8R
VOL_MAX,    //58   VOL_USB_L_OUT_CH9L
VOL_MIN,    //59   VOL_USB_L_OUT_CH10R
VOL_MAX,    //60   VOL_USB_L_OUT_CH11L
VOL_MIN,    //61   VOL_USB_L_OUT_CH12R
VOL_MAX,    //62   VOL_USB_L_OUT_SPDIFL
VOL_MIN,    //63   VOL_USB_L_OUT_SPDIFR
VOL_MIN,    //64   VOL_USB_R_OUT_CH1L
VOL_MAX,    //65   VOL_USB_R_OUT_CH2R
VOL_MIN,    //66   VOL_USB_R_OUT_CH3L
VOL_MAX,    //67   VOL_USB_R_OUT_CH4R
VOL_MIN,    //68   VOL_USB_R_OUT_CH5L
VOL_MAX,    //69   VOL_USB_R_OUT_CH6R
VOL_MIN,    //70   VOL_USB_R_OUT_CH7L
VOL_MAX,    //71   VOL_USB_R_OUT_CH8R
VOL_MIN,    //72   VOL_USB_R_OUT_CH9L
VOL_MAX,    //73   VOL_USB_R_OUT_CH10R
VOL_MIN,    //74   VOL_USB_R_OUT_CH11L
VOL_MAX,    //75   VOL_USB_R_OUT_CH12R
VOL_MIN,    //76   VOL_USB_R_OUT_SPDIFL
VOL_MAX,    //77   VOL_USB_R_OUT_SPDIFR
VOL_MAX,    //78   VOL_BLUETOOTH_L_OUT_CH1L
VOL_MIN,    //79   VOL_BLUETOOTH_L_OUT_CH2R
VOL_MAX,    //82   VOL_BLUETOOTH_L_OUT_CH3L
VOL_MIN,    //81   VOL_BLUETOOTH_L_OUT_CH4R
VOL_MAX,    //82   VOL_BLUETOOTH_L_OUT_CH5L
VOL_MIN,    //83   VOL_BLUETOOTH_L_OUT_CH6R
VOL_MAX,    //84   VOL_BLUETOOTH_L_OUT_CH7L
VOL_MIN,    //85   VOL_BLUETOOTH_L_OUT_CH8R
VOL_MAX,    //86   VOL_BLUETOOTH_L_OUT_CH9L
VOL_MIN,    //87   VOL_BLUETOOTH_L_OUT_CH10R
VOL_MAX,    //88   VOL_BLUETOOTH_L_OUT_CH11L
VOL_MIN,    //89   VOL_BLUETOOTH_L_OUT_CH12R
VOL_MAX,    //90   VOL_BLUETOOTH_L_OUT_SPDIFL
VOL_MIN,    //91   VOL_BLUETOOTH_L_OUT_SPDIFR
VOL_MIN,    //92   VOL_BLUETOOTH_R_OUT_CH1L
VOL_MAX,    //93   VOL_BLUETOOTH_R_OUT_CH2R
VOL_MIN,    //94   VOL_BLUETOOTH_R_OUT_CH3L
VOL_MAX,    //95   VOL_BLUETOOTH_R_OUT_CH4R
VOL_MIN,    //96   VOL_BLUETOOTH_R_OUT_CH5L
VOL_MAX,    //97   VOL_BLUETOOTH_R_OUT_CH6R
VOL_MIN,    //98   VOL_BLUETOOTH_R_OUT_CH7L
VOL_MAX,    //99   VOL_BLUETOOTH_R_OUT_CH8R
VOL_MIN,    //100  VOL_BLUETOOTH_R_OUT_CH9L
VOL_MAX,    //101  VOL_BLUETOOTH_R_OUT_CH10R
VOL_MIN,    //102  VOL_BLUETOOTH_R_OUT_CH11L
VOL_MAX,    //103  VOL_BLUETOOTH_R_OUT_CH12R
VOL_MIN,    //104  VOL_BLUETOOTH_R_OUT_SPDIFL
VOL_MAX,    //105  VOL_BLUETOOTH_R_OUT_SPDIFR
VOL_MAX,    //106   VOL_AUX_L_OUT_CH1L,
VOL_MIN,    //107   VOL_AUX_L_OUT_CH2R,
VOL_MAX,    //108   VOL_AUX_L_OUT_CH3L,
VOL_MIN,    //109   VOL_AUX_L_OUT_CH4R,
VOL_MAX,    //110   VOL_AUX_L_OUT_CH5L,
VOL_MIN,    //111   VOL_AUX_L_OUT_CH6R,
VOL_MAX,    //112   VOL_AUX_L_OUT_CH7L,
VOL_MIN,    //113   VOL_AUX_L_OUT_CH8R,
VOL_MAX,    //114   VOL_AUX_L_OUT_CH9L,
VOL_MIN,    //115   VOL_AUX_L_OUT_CH10R,
VOL_MAX,    //116   VOL_AUX_L_OUT_CH11L,
VOL_MIN,    //117   VOL_AUX_L_OUT_CH12R,
VOL_MAX,    //118   VOL_AUX_L_OUT_SPDIFL,
VOL_MIN,    //119   VOL_AUX_L_OUT_SPDIFR,
VOL_MIN,    //120   VOL_AUX_R_OUT_CH1L,
VOL_MAX,    //121   VOL_AUX_R_OUT_CH2R,
VOL_MIN,    //122   VOL_AUX_R_OUT_CH3L,
VOL_MAX,    //123   VOL_AUX_R_OUT_CH4R,
VOL_MIN,    //124   VOL_AUX_R_OUT_CH5L,
VOL_MAX,    //125   VOL_AUX_R_OUT_CH6R,
VOL_MIN,    //126   VOL_AUX_R_OUT_CH7L,
VOL_MAX,    //127   VOL_AUX_R_OUT_CH8R,
VOL_MIN,    //128   VOL_AUX_R_OUT_CH9L,
VOL_MAX,    //129   VOL_AUX_R_OUT_CH10R,
VOL_MIN,    //130   VOL_AUX_R_OUT_CH11L,
VOL_MAX,    //131   VOL_AUX_R_OUT_CH12R,
VOL_MIN,    //132   VOL_AUX_R_OUT_SPDIFL,
VOL_MAX,    //133   VOL_AUX_R_OUT_SPDIFR,
VOL_MAX,    //134   VOL_RADIO_L_OUT_CH1L,
VOL_MIN,    //135   VOL_RADIO_L_OUT_CH2R,
VOL_MAX,    //136   VOL_RADIO_L_OUT_CH3L,
VOL_MIN,    //137   VOL_RADIO_L_OUT_CH4R,
VOL_MAX,    //138   VOL_RADIO_L_OUT_CH5L,
VOL_MIN,    //139   VOL_RADIO_L_OUT_CH6R,
VOL_MAX,    //140   VOL_RADIO_L_OUT_CH7L,
VOL_MIN,    //141   VOL_RADIO_L_OUT_CH8R,
VOL_MAX,    //142   VOL_RADIO_L_OUT_CH9L,
VOL_MIN,    //143   VOL_RADIO_L_OUT_CH10R,
VOL_MAX,    //144   VOL_RADIO_L_OUT_CH11L,
VOL_MIN,    //145   VOL_RADIO_L_OUT_CH12R,
VOL_MAX,    //146   VOL_RADIO_L_OUT_SPDIFL,
VOL_MIN,    //147   VOL_RADIO_L_OUT_SPDIFR,
VOL_MIN,    //148   VOL_RADIO_R_OUT_CH1L,
VOL_MAX,    //149   VOL_RADIO_R_OUT_CH2R,
VOL_MIN,    //150   VOL_RADIO_R_OUT_CH3L,
VOL_MAX,    //151   VOL_RADIO_R_OUT_CH4R,
VOL_MIN,    //152   VOL_RADIO_R_OUT_CH5L,
VOL_MAX,    //153   VOL_RADIO_R_OUT_CH6R,
VOL_MIN,    //154   VOL_RADIO_R_OUT_CH7L,
VOL_MAX,    //155   VOL_RADIO_R_OUT_CH8R,
VOL_MIN,    //156   VOL_RADIO_R_OUT_CH9L,
VOL_MAX,    //157   VOL_RADIO_R_OUT_CH10R,
VOL_MIN,    //158   VOL_RADIO_R_OUT_CH11L,
VOL_MAX,    //159   VOL_RADIO_R_OUT_CH12R,
VOL_MIN,    //160   VOL_RADIO_R_OUT_SPDIFL,
VOL_MAX,    //161   VOL_RADIO_R_OUT_SPDIFR,
VOL_MAX,    //162   VOL_SPDIF_L_OUT_CH1L,
VOL_MIN,    //163   VOL_SPDIF_L_OUT_CH2R,
VOL_MAX,    //164   VOL_SPDIF_L_OUT_CH3L,
VOL_MIN,    //165   VOL_SPDIF_L_OUT_CH4R,
VOL_MAX,    //166   VOL_SPDIF_L_OUT_CH5L,
VOL_MIN,    //167   VOL_SPDIF_L_OUT_CH6R,
VOL_MAX,    //168   VOL_SPDIF_L_OUT_CH7L,
VOL_MIN,    //169   VOL_SPDIF_L_OUT_CH8R,
VOL_MAX,    //170   VOL_SPDIF_L_OUT_CH9L,
VOL_MIN,    //171   VOL_SPDIF_L_OUT_CH10R,
VOL_MAX,    //172   VOL_SPDIF_L_OUT_CH11L,
VOL_MIN,    //173   VOL_SPDIF_L_OUT_CH12R,
VOL_MAX,    //174   VOL_SPDIF_L_OUT_SPDIFL,
VOL_MIN,    //175   VOL_SPDIF_L_OUT_SPDIFR,
VOL_MIN,    //176   VOL_SPDIF_R_OUT_CH1L,
VOL_MAX,    //177   VOL_SPDIF_R_OUT_CH2R,
VOL_MIN,    //178   VOL_SPDIF_R_OUT_CH3L,
VOL_MAX,    //179   VOL_SPDIF_R_OUT_CH4R,
VOL_MIN,    //180   VOL_SPDIF_R_OUT_CH5L,
VOL_MAX,    //181   VOL_SPDIF_R_OUT_CH6R,
VOL_MIN,    //182   VOL_SPDIF_R_OUT_CH7L,
VOL_MAX,    //183   VOL_SPDIF_R_OUT_CH8R,
VOL_MIN,    //184   VOL_SPDIF_R_OUT_CH9L,
VOL_MAX,    //185   VOL_SPDIF_R_OUT_CH10R,
VOL_MIN,    //186   VOL_SPDIF_R_OUT_CH11L,
VOL_MAX,    //187   VOL_SPDIF_R_OUT_CH12R,
VOL_MIN,    //188   VOL_SPDIF_R_OUT_SPDIFL,
VOL_MAX,    //189   VOL_SPDIF_R_OUT_SPDIFR,
VOL_MAX,    //190   VOL_MIC_L_OUT_CH1L,
VOL_MIN,    //191   VOL_MIC_L_OUT_CH2R,
VOL_MAX,    //192   VOL_MIC_L_OUT_CH3L,
VOL_MIN,    //193   VOL_MIC_L_OUT_CH4R,
VOL_MAX,    //194   VOL_MIC_L_OUT_CH5L,
VOL_MIN,    //195   VOL_MIC_L_OUT_CH6R,
VOL_MAX,    //196   VOL_MIC_L_OUT_CH7L,
VOL_MIN,    //197   VOL_MIC_L_OUT_CH8R,
VOL_MAX,    //198   VOL_MIC_L_OUT_CH9L,
VOL_MIN,    //199   VOL_MIC_L_OUT_CH10R,
VOL_MAX,    //200   VOL_MIC_L_OUT_CH11L,
VOL_MIN,    //201   VOL_MIC_L_OUT_CH12R,
VOL_MAX,    //202   VOL_MIC_L_OUT_SPDIFL,
VOL_MIN,    //203   VOL_MIC_L_OUT_SPDIFR,
VOL_MIN,    //204   VOL_MIC_R_OUT_CH1L,
VOL_MAX,    //205   VOL_MIC_R_OUT_CH2R,
VOL_MIN,    //206   VOL_MIC_R_OUT_CH3L,
VOL_MAX,    //207   VOL_MIC_R_OUT_CH4R,
VOL_MIN,    //208   VOL_MIC_R_OUT_CH5L,
VOL_MAX,    //209   VOL_MIC_R_OUT_CH6R,
VOL_MIN,    //210   VOL_MIC_R_OUT_CH7L,
VOL_MAX,    //211   VOL_MIC_R_OUT_CH8R,
VOL_MIN,    //212   VOL_MIC_R_OUT_CH9L,
VOL_MAX,    //213   VOL_MIC_R_OUT_CH10R,
VOL_MIN,    //214   VOL_MIC_R_OUT_CH11L,
VOL_MAX,    //215   VOL_MIC_R_OUT_CH12R,
VOL_MIN,    //216   VOL_MIC_R_OUT_SPDIFL,
VOL_MAX,    //217   VOL_MIC_R_OUT_SPDIFR,
VOL_MIN,    //218   VOL_BEEP,
VOL_MAX,    //219   VOL_BEEP_OUT_CH1L,
VOL_MAX,    //220   VOL_BEEP_OUT_CH2R,
VOL_MAX,    //221   VOL_BEEP_OUT_CH3L,
VOL_MAX,    //222   VOL_BEEP_OUT_CH4R,
VOL_MAX,    //223   VOL_BEEP_OUT_CH5L,
VOL_MAX,    //224   VOL_BEEP_OUT_CH6R,
VOL_MAX,    //225   VOL_BEEP_OUT_CH7L,
VOL_MAX,    //226   VOL_BEEP_OUT_CH8R,
VOL_MAX,    //227   VOL_BEEP_OUT_CH9L,
VOL_MAX,    //228   VOL_BEEP_OUT_CH10R,
VOL_MAX,    //229   VOL_BEEP_OUT_CH11L,
VOL_MAX,    //230   VOL_BEEP_OUT_CH12R,
VOL_MAX,    //231   VOL_BEEP_OUT_SPDIFL,
VOL_MAX,    //232   VOL_BEEP_OUT_SPDIFR,

VOL_MIN,    //233 VOL_NOISE
VOL_MAX,    //234 VOL_NOISE_OUT_CH1L
VOL_MAX,    //235 VOL_NOISE_OUT_CH2R
VOL_MAX,    //236 VOL_NOISE_OUT_CH3L
VOL_MAX,    //237 VOL_NOISE_OUT_CH4R
VOL_MAX,    //238 VOL_NOISE_OUT_CH5L
VOL_MAX,    //239 VOL_NOISE_OUT_CH6R
VOL_MAX,    //240 VOL_NOISE_OUT_CH7L
VOL_MAX,    //241 VOL_NOISE_OUT_CH8R
VOL_MAX,    //242 VOL_NOISE_OUT_CH9L
VOL_MAX,    //243 VOL_NOISE_OUT_CH10R
VOL_MAX,    //244 VOL_NOISE_OUT_CH11L
VOL_MAX,    //245 VOL_NOISE_OUT_CH12R
VOL_MAX,    //246 VOL_NOISE_OUT_SPDIFL
VOL_MAX     //247 VOL_NOISE_OUT_SPDIFR
};


const uint16_t DSP_CH_EQ_ADDR[NUM_ELEM_EQ_CH * NUM_ELEM_EQ_CH_BAND] = {
//CH1L
ADDR_EQ_CH1L_ST0_B2,          //0
ADDR_EQ_CH1L_ST1_B2,          //1
ADDR_EQ_CH1L_ST2_B2,          //2
ADDR_EQ_CH1L_ST3_B2,          //3
ADDR_EQ_CH1L_ST4_B2,          //4
ADDR_EQ_CH1L_ST5_B2,          //5
ADDR_EQ_CH1L_ST6_B2,          //6
ADDR_EQ_CH1L_ST7_B2,          //7
ADDR_EQ_CH1L_ST8_B2,          //8
ADDR_EQ_CH1L_ST9_B2,          //9
ADDR_EQ_CH1L_ST10_B2,         //10
ADDR_EQ_CH1L_ST11_B2,         //11
ADDR_EQ_CH1L_ST12_B2,         //12
ADDR_EQ_CH1L_ST13_B2,         //13
ADDR_EQ_CH1L_ST14_B2,         //14
//CH2R
ADDR_EQ_CH2R_ST0_B2,          //0
ADDR_EQ_CH2R_ST1_B2,          //1
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
ADDR_EQ_SPDIF_R_ST8_B2,          //8
ADDR_EQ_SPDIF_R_ST9_B2,          //9
ADDR_EQ_SPDIF_R_ST10_B2,         //10
ADDR_EQ_SPDIF_R_ST11_B2,         //11
ADDR_EQ_SPDIF_R_ST12_B2,         //12
ADDR_EQ_SPDIF_R_ST13_B2,         //13
ADDR_EQ_SPDIF_R_ST14_B2,         //14
};

/*
//CROSSOVER
 */
const short  CROSSOVER_DSP_ADDR[NUM_ELEM_CROSSOVER*2] = {
ADDR_CROSSOVER_CH1L_ST0_B2,      //2     LOW PASS OK
ADDR_CROSSOVER_CH1L_ST5_B2,      //3     HI  PASS
ADDR_CROSSOVER_CH2R_ST0_B2,      //4     LOW PASS OK
ADDR_CROSSOVER_CH2R_ST5_B2,      //5     HI  PASS
ADDR_CROSSOVER_CH3L_ST0_B2,      //6     LOW PASS OK
ADDR_CROSSOVER_CH3L_ST5_B2,      //7     HI  PASS
ADDR_CROSSOVER_CH4R_ST0_B2,      //8     LOW PASS OK
ADDR_CROSSOVER_CH4R_ST5_B2,      //9     HI  PASS
ADDR_CROSSOVER_CH5L_ST0_B2,      //10    LOW PASS OK
ADDR_CROSSOVER_CH5L_ST5_B2,      //11    HI  PASS
ADDR_CROSSOVER_CH6R_ST0_B2,      //12    LOW PASS OK
ADDR_CROSSOVER_CH6R_ST5_B2,      //13    HI  PASS
ADDR_CROSSOVER_CH7L_ST0_B2,      //14    LOW PASS OK
ADDR_CROSSOVER_CH7L_ST5_B2,      //15    HI  PASS
ADDR_CROSSOVER_CH8R_ST0_B2,      //16    LOW PASS BAD
ADDR_CROSSOVER_CH8R_ST5_B2,      //17    HI  PASS
ADDR_CROSSOVER_CH9L_ST0_B2,      //18    LOW PASS BAD
ADDR_CROSSOVER_CH9L_ST5_B2,      //19    HI  PASS
ADDR_CROSSOVER_CH10R_ST0_B2,     //20    LOW PASS BAD
ADDR_CROSSOVER_CH10R_ST5_B2,     //21    HI  PASS
ADDR_CROSSOVER_CH11L_ST0_B2,     //22    LOW PASS
ADDR_CROSSOVER_CH11L_ST5_B2,     //23    HI  PASS
ADDR_CROSSOVER_CH12R_ST0_B2,     //24    LOW PASS
ADDR_CROSSOVER_CH12R_ST5_B2,     //25    HI  PASS
ADDR_CROSSOVER_SPDIF_L_ST0_B2,   //26    LOW PASS
ADDR_CROSSOVER_SPDIF_L_ST5_B2,   //27    HI  PASS
ADDR_CROSSOVER_SPDIF_R_ST0_B2,   //28    LOW PASS
ADDR_CROSSOVER_SPDIF_R_ST5_B2,   //29    HI  PASS
};


static const short  INVERT_DEFAULT[NUM_ELEM_INVERT] = {  //ADAU1962
OFF,                            //0    NOT USED
OFF,                            //1    CH 1 L
OFF,                            //2    CH 2 R
OFF,                            //3    CH 3 L
OFF,                            //4    CH 4 R
OFF,                            //5    CH 5 L
OFF,                            //6    CH 6 R
OFF,                            //7    CH 7 L
OFF,                            //8    CH 8 R
OFF,                            //9    CH 9 L
OFF,                            //10   CH 10 R
OFF,                            //11   CH 11 L
OFF,                            //12   CH 12 R
OFF,                            //13   CH SPDIF L
OFF,                            //14   CH SPDIF R
OFF,                            //15   USB L
OFF,                            //16   USB R
OFF,                            //17   BLUETOOTH L
OFF,                            //18   BLUETOOTH R
OFF,                            //19   AUX L
OFF,                            //20   AUX R
OFF,                            //21   RADIO L
OFF,                            //22   RADIO R
OFF,                            //23   SPDIF L
OFF,                            //24   SPDIF R
OFF,                            //25   MIC L
OFF,                            //26   MIC R
};


static const short  PHATSTEREO_DEFAULT[NUM_ELEM_PHATSTEREO*2] = {
//LEVEL   FREQ
  10,      1500,    //0   PHAT STEREO USB
  10,      1500,    //1   PHAT STEREO BLUETOOTH
  10,      1500,    //3   PHAT STEREO RADIO
  10,      1500,    //4   PHAT STEREO RADIO
  10,      1500,    //5   PHAT STEREO SPDIF
  10,      1500,    //6   PHAT STEREO MIC
};

static const short  WIDESTEREO_DEFAULT[NUM_ELEM_WIDESTEREO] = {
//LEVEL
  0,                //0   WIDE STEREO USB
  0,                //1   WIDE STEREO BLUETOOTH
  0,                //3   WIDE STEREO RADIO
  0,                //4   WIDE STEREO RADIO
  0,                //5   WIDE STEREO SPDIF
  0,                //6   WIDE STEREO MIC
};

static const short  SUPPERBASS_DEFAULT[NUM_ELEM_SUPPERBASS*4] = {
//ON/OFF  LEVEL    FREQ    INTESIV
  0,       12,      50,     13,    //0   SUPPERBASS USB
  0,       12,      50,     13,    //1   SUPPERBASS BLUETOOTH
  0,       12,      50,     13,    //3   SUPPERBASS RADIO
  0,       12,      50,     13,    //4   SUPPERBASS RADIO
  0,       12,      50,     13,    //5   SUPPERBASS SPDIF
  0,       12,      50,     13,    //6   SUPPERBASS MIC
};


static const short  LOUDNESS_DEFAULT[NUM_ELEM_LOUDNESS*4] = {
//FreqLP   LevelLP   FreqHP    LevelHP
  15,      50,        14000,    50,    //0   LOUDNESSS USB
  15,      50,        14000,    50,    //1   LOUDNESSS BLUETOOTH
  15,      50,        14000,    50,    //2   LOUDNESSS AUX
  15,      50,        14000,    50,    //3   LOUDNESSS RADIO
  15,      50,        14000,    50,    //4   LOUDNESSS SPDIF
  15,      50,        14000,    50,    //5   LOUDNESSS MIC
};


static const short  LIMITER_DEFAULT[NUM_ELEM_LIMITER*3] = {
//THRESHOLD     RMS         DECAY
  50,           5,          2,     //0     CH 1L
  50,           5,          2,     //1     CH 2R
  50,           5,          2,     //2     CH 3L
  50,           5,          2,     //3     CH 4R
  50,           5,          2,     //4     CH 5L
  50,           5,          2,     //5     CH 6R
  50,           5,          2,     //6     CH 7L
  50,           5,          2,     //7     CH 8R
  50,           5,          2,     //8     CH 9L
  50,           5,          2,     //9     CH 10R
  50,           5,          2,     //10    CH 11L
  50,           5,          2,     //11    CH 12R
  50,           5,          2,     //12    CH 13L
  50,           5,          2,     //13    CH 14R
};


static const short  EQ_SOURCE_DEFAULT[NUM_ELEM_EQ_CENTR] = {
60,       //0
260,       //1
800,       //2
4000,       //3
16000,       //4
};

static const short  EQ_CH_DEFAULT[NUM_ELEM_EQ_CH] = {
//FREQ
25,      //0
40,     //1
60,     //2
96,     //3
160,     //4
260,     //5
425,     //6
700,     //7
1100,    //8
1700,    //9
2700,    //10
4300,    //11
7300,    //12
12000,   //13
18000,   //14
};

int8_t GainDefPresetFlat = 0;
const int16_t  DefPresetFlat [NUM_ELEM_EQ_CENTR*2] = {
//BOOST     Q
  0,        150,     //0   20
  0,        150,     //1   35
  0,        150,     //2   48
  0,        150,     //3   50
  0,        150,     //4   63
  0,        150,     //5   80
  0,        150,     //6   100
  0,        150,     //7   125
  0,        150,     //8   160
  0,        150,     //9   200
  0,        150,     //10  250
  0,        150,     //11  315
  0,        150,     //12  400
  0,        150,     //13  630
  0,        150,     //14  800
  0,        150,     //15  1000
  0,        150,     //16  1250
  0,        150,     //17  1600
  0,        150,     //18  2000
  0,        150,     //19  2500
  0,        150,     //20  3150
  0,        150,     //21  4000
  0,        150,     //22  6300
  0,        150,     //23  8000
  0,        150,     //24  10000
  0,        150,     //25  12500
  0,        150,     //26  16000
  0,        150,     //27  18000
};

int8_t GainDefPressetBass = -5;
const float  DefPressetBass [NUM_ELEM_EQ_CENTR*2] = {
//BOOST     Q
  400,      150,     //0   20
  400,      150,     //1   35
  400,      150,     //2   48
  300,      150,     //3   50
  200,      150,     //4   63
  100,      150,     //5   80
  000,      150,     //6   100
 -100,      150,     //7   125
 -200,      150,     //8   160
 -100,      150,     //9   200
  000,      150,     //10  250
  000,      150,     //11  315
  000,      150,     //12  400
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
		  0,        150,     //20  3150
		  0,        150,     //21  4000
		  0,        150,     //22  6300
		  0,        150,     //23  8000
		  0,        150,     //24  10000
		  0,        150,     //25  12500
		  0,        150,     //26  16000
		  0,        150,     //27  18000
};


const uint8_t  DefaultPresetSoftHigh [NUM_ELEM_EQ_CENTR*2] = {
     //BOOST*0,01   Q*0,01
		  0,        150,     //0   20
		  0,        150,     //1   35
		  0,        150,     //2   48
		  0,        150,     //3   50
		  0,        150,     //4   63
		  0,        150,     //5   80
		  0,        150,     //6   100
		  0,        150,     //7   125
		  0,        150,     //8   160
		  0,        150,     //9   200
		  0,        150,     //10  250
		  0,        150,     //11  315
		  0,        150,     //12  400
		  0,        150,     //13  630
		  0,        150,     //14  800
		  0,        150,     //15  1000
		  0,        150,     //16  1250
		  0,        150,     //17  1600
		  0,        150,     //18  2000
		  0,        150,     //19  2500
		  0,        150,     //20  3150
		  0,        150,     //21  4000
		  0,        150,     //22  6300
		  0,        150,     //23  8000
		  0,        150,     //24  10000
		  0,        150,     //25  12500
		  0,        150,     //26  16000
		  0,        150,     //27  18000
};




static const uint8_t  DEFAULT_CH_GROUP[NUM_ELEM_EQ_CH] = {
		1,
		0,
		3,
		2,
		5,
		4,
		7,
		6,
		9,
		8,
		11,
		10,
		13,
		12,
};

static const uint8_t  DEFAULT_DELAY_GROUP[NUM_ELEM_EQ_CH] = {
		1,
		1,
		2,
		2,
		3,
		3,
		4,
		4,
		5,
		5,
		6,
		6,
		7,
		7,
};

static const uint16_t  DEFAULT_DSP_SETTINGS[64] = {
Main_Preset,            // 0 EqStandardPresets
Main_Preset,            // 1 DspPresset
VolumControlOnLoudness, // 2 Vo 2lumeControlMode
OFF,                    // 3 Selfbot
1,                      // 4 DspInitialization
SoursUsb,               // 5 SoundSource
ON,                     // 6 Sound_Routing_USB
ON,                     // 7 Sound_Routing_Bluetooth
ON,                     // 8 Sound_Routing_Aux
ON,                     // 9 Sound_Routing_Radio
ON,                     // 10 Sound_Routing_Spdif
ON,                     // 11 Sound_Routing_Mic
ON,                     // 12 Preset_Routing_User1
ON,                     // 13 Preset_Routing_User2
ON,                     // 14 Preset_Routing_User3
ON,                     // 15 Preset_Routing_Flat
ON,                     // 16 Preset_Routing_Bass
ON,                     // 17 Preset_Routing_BassExtreme
ON,                     // 18 Preset_Routing_BassAndHigh
ON,                     // 19 Preset_Routing_Classic
ON,                     // 20 Preset_Routing_Dancing
ON,                     // 21 Preset_Routing_Speaker
ON,                     // 22 Preset_Routing_Live
ON,                     // 23 Preset_Routing_Medium
ON,                     // 24 Preset_Routing_Soft
ON,                     // 25 Preset_Routing_SoftBass
ON,                     // 26 Preset_Routing_SoftHigh
ON,                     // 27 LoudnessUsb
ON,                     // 28 LoudnessBluetooth
ON,                     // 29 LoudnessRadio
ON,                     // 30 LoudnessSpdif
ON,                     // 31 LoudnessMic
OFF,                    // 32 LevelDetector
20,                     // 33 VolumLevelPoewrUp
DEFAULT_HYS_TEMP,       // 34 TempHysteresis
DEFAULT_OS_TEMP,        // 35 TempOS
2,                      // 36 Rear Camera On Volume Default
20,                     // 37 Rear Camera minimum volume
};


static const uint16_t  DEFAULT_CROSSOVER_FREQ[NUM_ELEM_CROSSOVER_TYPE] = {
100,          //0 HIPASS
5000          //1 LOWPASS
};

static const uint8_t  DEFAULT_CROSSOVER_TYPE[NUM_ELEM_CROSSOVER_TYPE] = {
BUTTERWORTH_HP, //0 HIPASS
BUTTERWORTH_LP  //1 LOWPASS
};



#endif /* MODULE_DSP_DSP_ELEMENTADDRES_H_ */
