alekssandr89/Dixom-m/Firmware/Dixom_m_Base_Inspiration/Dixom/Module/DSP/SigmaStudio/Inc_ADAU1452/Base_DSP_ADAU1452_REG.h

/*
 * File:           E:\Project\Git\DSTM\dixom_m_base_frimware\Dixom_m_Base_Frimware\Dixom\Module\DSP\SigmaStudio\Inc_ADAU1452\Base_DSP_ADAU1452_REG.h
 *
 * Created:        Thursday, March 3, 2022 11:48:01 AM
 * Description:    Base:DSP_ADAU1452 control register definitions.
 *
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
 * This software may only be used to program products purchased from
 * Analog Devices for incorporation by you into audio products that
 * are intended for resale to audio product end users. This software
 * may not be distributed whole or in any part to third parties.
 *
 * Copyright ©2022 Analog Devices, Inc. All rights reserved.
 */
#ifndef __BASE_DSP_ADAU1452_REG_H__
#define __BASE_DSP_ADAU1452_REG_H__


/* PLL_CTRL0  - Registers (DSP_ADAU1452) */
#define REG_PLL_CTRL0_DSP_ADAU1452_ADDR           0xF000
#define REG_PLL_CTRL0_DSP_ADAU1452_BYTE           2
#define REG_PLL_CTRL0_DSP_ADAU1452_VALUE          0x60

/* PLL_CTRL1  - Registers (DSP_ADAU1452) */
#define REG_PLL_CTRL1_DSP_ADAU1452_ADDR           0xF001
#define REG_PLL_CTRL1_DSP_ADAU1452_BYTE           2
#define REG_PLL_CTRL1_DSP_ADAU1452_VALUE          0x3

/* PLL_CLK_SRC  - Registers (DSP_ADAU1452) */
#define REG_PLL_CLK_SRC_DSP_ADAU1452_ADDR         0xF002
#define REG_PLL_CLK_SRC_DSP_ADAU1452_BYTE         2
#define REG_PLL_CLK_SRC_DSP_ADAU1452_VALUE        0x1

/* PLL_ENABLE  - Registers (DSP_ADAU1452) */
#define REG_PLL_ENABLE_DSP_ADAU1452_ADDR          0xF003
#define REG_PLL_ENABLE_DSP_ADAU1452_BYTE          2
#define REG_PLL_ENABLE_DSP_ADAU1452_VALUE         0x1

/* PLL_LOCK  - Registers (DSP_ADAU1452) */
#define REG_PLL_LOCK_DSP_ADAU1452_ADDR            0xF004
#define REG_PLL_LOCK_DSP_ADAU1452_BYTE            0
#define REG_PLL_LOCK_DSP_ADAU1452_VALUE           0x1

/* MCLK_OUT  - Registers (DSP_ADAU1452) */
#define REG_MCLK_OUT_DSP_ADAU1452_ADDR            0xF005
#define REG_MCLK_OUT_DSP_ADAU1452_BYTE            2
#define REG_MCLK_OUT_DSP_ADAU1452_VALUE           0x7

/* PLL_WATCHDOG  - Registers (DSP_ADAU1452) */
#define REG_PLL_WATCHDOG_DSP_ADAU1452_ADDR        0xF006
#define REG_PLL_WATCHDOG_DSP_ADAU1452_BYTE        2
#define REG_PLL_WATCHDOG_DSP_ADAU1452_VALUE       0x1

/* CLK_GEN1_M  - Registers (DSP_ADAU1452) */
#define REG_CLK_GEN1_M_DSP_ADAU1452_ADDR          0xF020
#define REG_CLK_GEN1_M_DSP_ADAU1452_BYTE          2
#define REG_CLK_GEN1_M_DSP_ADAU1452_VALUE         0x6

/* CLK_GEN1_N  - Registers (DSP_ADAU1452) */
#define REG_CLK_GEN1_N_DSP_ADAU1452_ADDR          0xF021
#define REG_CLK_GEN1_N_DSP_ADAU1452_BYTE          2
#define REG_CLK_GEN1_N_DSP_ADAU1452_VALUE         0x1

/* CLK_GEN2_M  - Registers (DSP_ADAU1452) */
#define REG_CLK_GEN2_M_DSP_ADAU1452_ADDR          0xF022
#define REG_CLK_GEN2_M_DSP_ADAU1452_BYTE          2
#define REG_CLK_GEN2_M_DSP_ADAU1452_VALUE         0x9

/* CLK_GEN2_N  - Registers (DSP_ADAU1452) */
#define REG_CLK_GEN2_N_DSP_ADAU1452_ADDR          0xF023
#define REG_CLK_GEN2_N_DSP_ADAU1452_BYTE          2
#define REG_CLK_GEN2_N_DSP_ADAU1452_VALUE         0x1

/* CLK_GEN3_M  - Registers (DSP_ADAU1452) */
#define REG_CLK_GEN3_M_DSP_ADAU1452_ADDR          0xF024
#define REG_CLK_GEN3_M_DSP_ADAU1452_BYTE          2
#define REG_CLK_GEN3_M_DSP_ADAU1452_VALUE         0x0

/* CLK_GEN3_N  - Registers (DSP_ADAU1452) */
#define REG_CLK_GEN3_N_DSP_ADAU1452_ADDR          0xF025
#define REG_CLK_GEN3_N_DSP_ADAU1452_BYTE          2
#define REG_CLK_GEN3_N_DSP_ADAU1452_VALUE         0x0

/* CLK_GEN3_SRC  - Registers (DSP_ADAU1452) */
#define REG_CLK_GEN3_SRC_DSP_ADAU1452_ADDR        0xF026
#define REG_CLK_GEN3_SRC_DSP_ADAU1452_BYTE        2
#define REG_CLK_GEN3_SRC_DSP_ADAU1452_VALUE       0xE

/* CLK_GEN3_LOCK  - Registers (DSP_ADAU1452) */
#define REG_CLK_GEN3_LOCK_DSP_ADAU1452_ADDR       0xF027
#define REG_CLK_GEN3_LOCK_DSP_ADAU1452_BYTE       0
#define REG_CLK_GEN3_LOCK_DSP_ADAU1452_VALUE      0x1

/* POWER_ENABLE0  - Registers (DSP_ADAU1452) */
#define REG_POWER_ENABLE0_DSP_ADAU1452_ADDR       0xF050
#define REG_POWER_ENABLE0_DSP_ADAU1452_BYTE       2
#define REG_POWER_ENABLE0_DSP_ADAU1452_VALUE      0x1FFF

/* POWER_ENABLE1  - Registers (DSP_ADAU1452) */
#define REG_POWER_ENABLE1_DSP_ADAU1452_ADDR       0xF051
#define REG_POWER_ENABLE1_DSP_ADAU1452_BYTE       2
#define REG_POWER_ENABLE1_DSP_ADAU1452_VALUE      0x1F

/* ASRC_INPUT0  - Registers (DSP_ADAU1452) */
#define REG_ASRC_INPUT0_DSP_ADAU1452_ADDR         0xF100
#define REG_ASRC_INPUT0_DSP_ADAU1452_BYTE         2
#define REG_ASRC_INPUT0_DSP_ADAU1452_VALUE        0x81

/* ASRC_INPUT1  - Registers (DSP_ADAU1452) */
#define REG_ASRC_INPUT1_DSP_ADAU1452_ADDR         0xF101
#define REG_ASRC_INPUT1_DSP_ADAU1452_BYTE         2
#define REG_ASRC_INPUT1_DSP_ADAU1452_VALUE        0x1

/* ASRC_INPUT2  - Registers (DSP_ADAU1452) */
#define REG_ASRC_INPUT2_DSP_ADAU1452_ADDR         0xF102
#define REG_ASRC_INPUT2_DSP_ADAU1452_BYTE         2
#define REG_ASRC_INPUT2_DSP_ADAU1452_VALUE        0xA1

/* ASRC_INPUT3  - Registers (DSP_ADAU1452) */
#define REG_ASRC_INPUT3_DSP_ADAU1452_ADDR         0xF103
#define REG_ASRC_INPUT3_DSP_ADAU1452_BYTE         2
#define REG_ASRC_INPUT3_DSP_ADAU1452_VALUE        0x41

/* ASRC_INPUT4  - Registers (DSP_ADAU1452) */
#define REG_ASRC_INPUT4_DSP_ADAU1452_ADDR         0xF104
#define REG_ASRC_INPUT4_DSP_ADAU1452_BYTE         2
#define REG_ASRC_INPUT4_DSP_ADAU1452_VALUE        0xB

/* ASRC_INPUT5  - Registers (DSP_ADAU1452) */
#define REG_ASRC_INPUT5_DSP_ADAU1452_ADDR         0xF105
#define REG_ASRC_INPUT5_DSP_ADAU1452_BYTE         2
#define REG_ASRC_INPUT5_DSP_ADAU1452_VALUE        0x4

/* ASRC_INPUT6  - Registers (DSP_ADAU1452) */
#define REG_ASRC_INPUT6_DSP_ADAU1452_ADDR         0xF106
#define REG_ASRC_INPUT6_DSP_ADAU1452_BYTE         2
#define REG_ASRC_INPUT6_DSP_ADAU1452_VALUE        0x5

/* ASRC_INPUT7  - Registers (DSP_ADAU1452) */
#define REG_ASRC_INPUT7_DSP_ADAU1452_ADDR         0xF107
#define REG_ASRC_INPUT7_DSP_ADAU1452_BYTE         2
#define REG_ASRC_INPUT7_DSP_ADAU1452_VALUE        0x3

/* ASRC_OUT_RATE0  - Registers (DSP_ADAU1452) */
#define REG_ASRC_OUT_RATE0_DSP_ADAU1452_ADDR      0xF140
#define REG_ASRC_OUT_RATE0_DSP_ADAU1452_BYTE      2
#define REG_ASRC_OUT_RATE0_DSP_ADAU1452_VALUE     0x5

/* ASRC_OUT_RATE1  - Registers (DSP_ADAU1452) */
#define REG_ASRC_OUT_RATE1_DSP_ADAU1452_ADDR      0xF141
#define REG_ASRC_OUT_RATE1_DSP_ADAU1452_BYTE      2
#define REG_ASRC_OUT_RATE1_DSP_ADAU1452_VALUE     0x5

/* ASRC_OUT_RATE2  - Registers (DSP_ADAU1452) */
#define REG_ASRC_OUT_RATE2_DSP_ADAU1452_ADDR      0xF142
#define REG_ASRC_OUT_RATE2_DSP_ADAU1452_BYTE      2
#define REG_ASRC_OUT_RATE2_DSP_ADAU1452_VALUE     0x5

/* ASRC_OUT_RATE3  - Registers (DSP_ADAU1452) */
#define REG_ASRC_OUT_RATE3_DSP_ADAU1452_ADDR      0xF143
#define REG_ASRC_OUT_RATE3_DSP_ADAU1452_BYTE      2
#define REG_ASRC_OUT_RATE3_DSP_ADAU1452_VALUE     0x5

/* ASRC_OUT_RATE4  - Registers (DSP_ADAU1452) */
#define REG_ASRC_OUT_RATE4_DSP_ADAU1452_ADDR      0xF144
#define REG_ASRC_OUT_RATE4_DSP_ADAU1452_BYTE      2
#define REG_ASRC_OUT_RATE4_DSP_ADAU1452_VALUE     0x5

/* ASRC_OUT_RATE5  - Registers (DSP_ADAU1452) */
#define REG_ASRC_OUT_RATE5_DSP_ADAU1452_ADDR      0xF145
#define REG_ASRC_OUT_RATE5_DSP_ADAU1452_BYTE      2
#define REG_ASRC_OUT_RATE5_DSP_ADAU1452_VALUE     0x0

/* ASRC_OUT_RATE6  - Registers (DSP_ADAU1452) */
#define REG_ASRC_OUT_RATE6_DSP_ADAU1452_ADDR      0xF146
#define REG_ASRC_OUT_RATE6_DSP_ADAU1452_BYTE      2
#define REG_ASRC_OUT_RATE6_DSP_ADAU1452_VALUE     0x5

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
#define REG_FTDM_OUT52_DSP_ADAU1452_VALUE         0x0

/* FTDM_OUT53  - Registers (DSP_ADAU1452) */
#define REG_FTDM_OUT53_DSP_ADAU1452_ADDR          0xF3B5
#define REG_FTDM_OUT53_DSP_ADAU1452_BYTE          2
#define REG_FTDM_OUT53_DSP_ADAU1452_VALUE         0x0

/* FTDM_OUT54  - Registers (DSP_ADAU1452) */
#define REG_FTDM_OUT54_DSP_ADAU1452_ADDR          0xF3B6
#define REG_FTDM_OUT54_DSP_ADAU1452_BYTE          2
#define REG_FTDM_OUT54_DSP_ADAU1452_VALUE         0x0

/* FTDM_OUT55  - Registers (DSP_ADAU1452) */
#define REG_FTDM_OUT55_DSP_ADAU1452_ADDR          0xF3B7
#define REG_FTDM_OUT55_DSP_ADAU1452_BYTE          2
#define REG_FTDM_OUT55_DSP_ADAU1452_VALUE         0x0

/* FTDM_OUT56  - Registers (DSP_ADAU1452) */
#define REG_FTDM_OUT56_DSP_ADAU1452_ADDR          0xF3B8
#define REG_FTDM_OUT56_DSP_ADAU1452_BYTE          2
#define REG_FTDM_OUT56_DSP_ADAU1452_VALUE         0x0

/* FTDM_OUT57  - Registers (DSP_ADAU1452) */
#define REG_FTDM_OUT57_DSP_ADAU1452_ADDR          0xF3B9
#define REG_FTDM_OUT57_DSP_ADAU1452_BYTE          2
#define REG_FTDM_OUT57_DSP_ADAU1452_VALUE         0x0

/* FTDM_OUT58  - Registers (DSP_ADAU1452) */
#define REG_FTDM_OUT58_DSP_ADAU1452_ADDR          0xF3BA
#define REG_FTDM_OUT58_DSP_ADAU1452_BYTE          2
#define REG_FTDM_OUT58_DSP_ADAU1452_VALUE         0x0

/* FTDM_OUT59  - Registers (DSP_ADAU1452) */
#define REG_FTDM_OUT59_DSP_ADAU1452_ADDR          0xF3BB
#define REG_FTDM_OUT59_DSP_ADAU1452_BYTE          2
#define REG_FTDM_OUT59_DSP_ADAU1452_VALUE         0x0

/* FTDM_OUT60  - Registers (DSP_ADAU1452) */
#define REG_FTDM_OUT60_DSP_ADAU1452_ADDR          0xF3BC
#define REG_FTDM_OUT60_DSP_ADAU1452_BYTE          2
#define REG_FTDM_OUT60_DSP_ADAU1452_VALUE         0x0

/* FTDM_OUT61  - Registers (DSP_ADAU1452) */
#define REG_FTDM_OUT61_DSP_ADAU1452_ADDR          0xF3BD
#define REG_FTDM_OUT61_DSP_ADAU1452_BYTE          2
#define REG_FTDM_OUT61_DSP_ADAU1452_VALUE         0x0

/* FTDM_OUT62  - Registers (DSP_ADAU1452) */
#define REG_FTDM_OUT62_DSP_ADAU1452_ADDR          0xF3BE
#define REG_FTDM_OUT62_DSP_ADAU1452_BYTE          2
#define REG_FTDM_OUT62_DSP_ADAU1452_VALUE         0x0

/* FTDM_OUT63  - Registers (DSP_ADAU1452) */
#define REG_FTDM_OUT63_DSP_ADAU1452_ADDR          0xF3BF
#define REG_FTDM_OUT63_DSP_ADAU1452_BYTE          2
#define REG_FTDM_OUT63_DSP_ADAU1452_VALUE         0x0

/* HIBERNATE  - Registers (DSP_ADAU1452) */
#define REG_HIBERNATE_DSP_ADAU1452_ADDR           0xF400
#define REG_HIBERNATE_DSP_ADAU1452_BYTE           2
#define REG_HIBERNATE_DSP_ADAU1452_VALUE          0x0

/* START_PULSE  - Registers (DSP_ADAU1452) */
#define REG_START_PULSE_DSP_ADAU1452_ADDR         0xF401
#define REG_START_PULSE_DSP_ADAU1452_BYTE         2
#define REG_START_PULSE_DSP_ADAU1452_VALUE        0x2

/* START_CORE  - Registers (DSP_ADAU1452) */
#define REG_START_CORE_DSP_ADAU1452_ADDR          0xF402
#define REG_START_CORE_DSP_ADAU1452_BYTE          2
#define REG_START_CORE_DSP_ADAU1452_VALUE         0x1

/* KILL_CORE  - Registers (DSP_ADAU1452) */
#define REG_KILL_CORE_DSP_ADAU1452_ADDR           0xF403
#define REG_KILL_CORE_DSP_ADAU1452_BYTE           2
#define REG_KILL_CORE_DSP_ADAU1452_VALUE          0x0

/* START_ADDRESS  - Registers (DSP_ADAU1452) */
#define REG_START_ADDRESS_DSP_ADAU1452_ADDR       0xF404
#define REG_START_ADDRESS_DSP_ADAU1452_BYTE       2
#define REG_START_ADDRESS_DSP_ADAU1452_VALUE      0x0

/* CORE_STATUS  - Registers (DSP_ADAU1452) */
#define REG_CORE_STATUS_DSP_ADAU1452_ADDR         0xF405
#define REG_CORE_STATUS_DSP_ADAU1452_BYTE         0
#define REG_CORE_STATUS_DSP_ADAU1452_VALUE        0x1

/* DEBUG_MODE  - Registers (DSP_ADAU1452) */
#define REG_DEBUG_MODE_DSP_ADAU1452_ADDR          0xF420
#define REG_DEBUG_MODE_DSP_ADAU1452_BYTE          2
#define REG_DEBUG_MODE_DSP_ADAU1452_VALUE         0x0

/* PANIC_CLEAR  - Registers (DSP_ADAU1452) */
#define REG_PANIC_CLEAR_DSP_ADAU1452_ADDR         0xF421
#define REG_PANIC_CLEAR_DSP_ADAU1452_BYTE         2
#define REG_PANIC_CLEAR_DSP_ADAU1452_VALUE        0x1

/* PANIC_PARITY_MASK  - Registers (DSP_ADAU1452) */
#define REG_PANIC_PARITY_MASK_DSP_ADAU1452_ADDR   0xF422
#define REG_PANIC_PARITY_MASK_DSP_ADAU1452_BYTE   2
#define REG_PANIC_PARITY_MASK_DSP_ADAU1452_VALUE  0x0

/* PANIC_SOFTWARE_MASK  - Registers (DSP_ADAU1452) */
#define REG_PANIC_SOFTWARE_MASK_DSP_ADAU1452_ADDR 0xF423
#define REG_PANIC_SOFTWARE_MASK_DSP_ADAU1452_BYTE 2
#define REG_PANIC_SOFTWARE_MASK_DSP_ADAU1452_VALUE 0x0

/* PANIC_WD_MASK  - Registers (DSP_ADAU1452) */
#define REG_PANIC_WD_MASK_DSP_ADAU1452_ADDR       0xF424
#define REG_PANIC_WD_MASK_DSP_ADAU1452_BYTE       2
#define REG_PANIC_WD_MASK_DSP_ADAU1452_VALUE      0x0

/* PANIC_STACK_MASK  - Registers (DSP_ADAU1452) */
#define REG_PANIC_STACK_MASK_DSP_ADAU1452_ADDR    0xF425
#define REG_PANIC_STACK_MASK_DSP_ADAU1452_BYTE    2
#define REG_PANIC_STACK_MASK_DSP_ADAU1452_VALUE   0x0

/* PANIC_LOOP_MASK  - Registers (DSP_ADAU1452) */
#define REG_PANIC_LOOP_MASK_DSP_ADAU1452_ADDR     0xF426
#define REG_PANIC_LOOP_MASK_DSP_ADAU1452_BYTE     2
#define REG_PANIC_LOOP_MASK_DSP_ADAU1452_VALUE    0x0

/* PANIC_FLAG  - Registers (DSP_ADAU1452) */
#define REG_PANIC_FLAG_DSP_ADAU1452_ADDR          0xF427
#define REG_PANIC_FLAG_DSP_ADAU1452_BYTE          0
#define REG_PANIC_FLAG_DSP_ADAU1452_VALUE         0x0

/* PANIC_CODE  - Registers (DSP_ADAU1452) */
#define REG_PANIC_CODE_DSP_ADAU1452_ADDR          0xF428
#define REG_PANIC_CODE_DSP_ADAU1452_BYTE          0
#define REG_PANIC_CODE_DSP_ADAU1452_VALUE         0x0

/* DECODE_OP0  - Registers (DSP_ADAU1452) */
#define REG_DECODE_OP0_DSP_ADAU1452_ADDR          0xF429
#define REG_DECODE_OP0_DSP_ADAU1452_BYTE          0
#define REG_DECODE_OP0_DSP_ADAU1452_VALUE         0x0

/* DECODE_OP1  - Registers (DSP_ADAU1452) */
#define REG_DECODE_OP1_DSP_ADAU1452_ADDR          0xF42A
#define REG_DECODE_OP1_DSP_ADAU1452_BYTE          0
#define REG_DECODE_OP1_DSP_ADAU1452_VALUE         0x0

/* DECODE_OP2  - Registers (DSP_ADAU1452) */
#define REG_DECODE_OP2_DSP_ADAU1452_ADDR          0xF42B
#define REG_DECODE_OP2_DSP_ADAU1452_BYTE          0
#define REG_DECODE_OP2_DSP_ADAU1452_VALUE         0x0

/* DECODE_OP3  - Registers (DSP_ADAU1452) */
#define REG_DECODE_OP3_DSP_ADAU1452_ADDR          0xF42C
#define REG_DECODE_OP3_DSP_ADAU1452_BYTE          0
#define REG_DECODE_OP3_DSP_ADAU1452_VALUE         0x0

/* EXECUTE_OP0  - Registers (DSP_ADAU1452) */
#define REG_EXECUTE_OP0_DSP_ADAU1452_ADDR         0xF42D
#define REG_EXECUTE_OP0_DSP_ADAU1452_BYTE         0
#define REG_EXECUTE_OP0_DSP_ADAU1452_VALUE        0x0

/* EXECUTE_OP1  - Registers (DSP_ADAU1452) */
#define REG_EXECUTE_OP1_DSP_ADAU1452_ADDR         0xF42E
#define REG_EXECUTE_OP1_DSP_ADAU1452_BYTE         0
#define REG_EXECUTE_OP1_DSP_ADAU1452_VALUE        0x0

/* EXECUTE_OP2  - Registers (DSP_ADAU1452) */
#define REG_EXECUTE_OP2_DSP_ADAU1452_ADDR         0xF42F
#define REG_EXECUTE_OP2_DSP_ADAU1452_BYTE         0
#define REG_EXECUTE_OP2_DSP_ADAU1452_VALUE        0x0

/* EXECUTE_OP3  - Registers (DSP_ADAU1452) */
#define REG_EXECUTE_OP3_DSP_ADAU1452_ADDR         0xF430
#define REG_EXECUTE_OP3_DSP_ADAU1452_BYTE         0
#define REG_EXECUTE_OP3_DSP_ADAU1452_VALUE        0x0

/* DECODE_COUNT  - Registers (DSP_ADAU1452) */
#define REG_DECODE_COUNT_DSP_ADAU1452_ADDR        0xF431
#define REG_DECODE_COUNT_DSP_ADAU1452_BYTE        0
#define REG_DECODE_COUNT_DSP_ADAU1452_VALUE       0x0

/* EXECUTE_COUNT  - Registers (DSP_ADAU1452) */
#define REG_EXECUTE_COUNT_DSP_ADAU1452_ADDR       0xF432
#define REG_EXECUTE_COUNT_DSP_ADAU1452_BYTE       0
#define REG_EXECUTE_COUNT_DSP_ADAU1452_VALUE      0x0

/* SOFTWARE_VALUE_0  - Registers (DSP_ADAU1452) */
#define REG_SOFTWARE_VALUE_0_DSP_ADAU1452_ADDR    0xF433
#define REG_SOFTWARE_VALUE_0_DSP_ADAU1452_BYTE    0
#define REG_SOFTWARE_VALUE_0_DSP_ADAU1452_VALUE   0x0

/* SOFTWARE_VALUE_1  - Registers (DSP_ADAU1452) */
#define REG_SOFTWARE_VALUE_1_DSP_ADAU1452_ADDR    0xF434
#define REG_SOFTWARE_VALUE_1_DSP_ADAU1452_BYTE    0
#define REG_SOFTWARE_VALUE_1_DSP_ADAU1452_VALUE   0x0

/* WATCHDOG_MAXCOUNT  - Registers (DSP_ADAU1452) */
#define REG_WATCHDOG_MAXCOUNT_DSP_ADAU1452_ADDR   0xF443
#define REG_WATCHDOG_MAXCOUNT_DSP_ADAU1452_BYTE   2
#define REG_WATCHDOG_MAXCOUNT_DSP_ADAU1452_VALUE  0x0

/* WATCHDOG_PRESCALE  - Registers (DSP_ADAU1452) */
#define REG_WATCHDOG_PRESCALE_DSP_ADAU1452_ADDR   0xF444
#define REG_WATCHDOG_PRESCALE_DSP_ADAU1452_BYTE   2
#define REG_WATCHDOG_PRESCALE_DSP_ADAU1452_VALUE  0x0

/* BLOCKINT_EN  - Registers (DSP_ADAU1452) */
#define REG_BLOCKINT_EN_DSP_ADAU1452_ADDR         0xF450
#define REG_BLOCKINT_EN_DSP_ADAU1452_BYTE         2
#define REG_BLOCKINT_EN_DSP_ADAU1452_VALUE        0x0

/* BLOCKINT_VALUE  - Registers (DSP_ADAU1452) */
#define REG_BLOCKINT_VALUE_DSP_ADAU1452_ADDR      0xF451
#define REG_BLOCKINT_VALUE_DSP_ADAU1452_BYTE      2
#define REG_BLOCKINT_VALUE_DSP_ADAU1452_VALUE     0x0

/* PROG_CNTR0  - Registers (DSP_ADAU1452) */
#define REG_PROG_CNTR0_DSP_ADAU1452_ADDR          0xF460
#define REG_PROG_CNTR0_DSP_ADAU1452_BYTE          0
#define REG_PROG_CNTR0_DSP_ADAU1452_VALUE         0x0

/* PROG_CNTR1  - Registers (DSP_ADAU1452) */
#define REG_PROG_CNTR1_DSP_ADAU1452_ADDR          0xF461
#define REG_PROG_CNTR1_DSP_ADAU1452_BYTE          0
#define REG_PROG_CNTR1_DSP_ADAU1452_VALUE         0x62F

/* PROG_CNTR_CLEAR  - Registers (DSP_ADAU1452) */
#define REG_PROG_CNTR_CLEAR_DSP_ADAU1452_ADDR     0xF462
#define REG_PROG_CNTR_CLEAR_DSP_ADAU1452_BYTE     2
#define REG_PROG_CNTR_CLEAR_DSP_ADAU1452_VALUE    0x0

/* PROG_CNTR_LENGTH0  - Registers (DSP_ADAU1452) */
#define REG_PROG_CNTR_LENGTH0_DSP_ADAU1452_ADDR   0xF463
#define REG_PROG_CNTR_LENGTH0_DSP_ADAU1452_BYTE   0
#define REG_PROG_CNTR_LENGTH0_DSP_ADAU1452_VALUE  0x0

/* PROG_CNTR_LENGTH1  - Registers (DSP_ADAU1452) */
#define REG_PROG_CNTR_LENGTH1_DSP_ADAU1452_ADDR   0xF464
#define REG_PROG_CNTR_LENGTH1_DSP_ADAU1452_BYTE   0
#define REG_PROG_CNTR_LENGTH1_DSP_ADAU1452_VALUE  0xAAF

/* PROG_CNTR_MAXLENGTH0  - Registers (DSP_ADAU1452) */
#define REG_PROG_CNTR_MAXLENGTH0_DSP_ADAU1452_ADDR 0xF465
#define REG_PROG_CNTR_MAXLENGTH0_DSP_ADAU1452_BYTE 0
#define REG_PROG_CNTR_MAXLENGTH0_DSP_ADAU1452_VALUE 0x0

/* PROG_CNTR_MAXLENGTH1  - Registers (DSP_ADAU1452) */
#define REG_PROG_CNTR_MAXLENGTH1_DSP_ADAU1452_ADDR 0xF466
#define REG_PROG_CNTR_MAXLENGTH1_DSP_ADAU1452_BYTE 0
#define REG_PROG_CNTR_MAXLENGTH1_DSP_ADAU1452_VALUE 0xAC5

/* MP0_MODE  - Registers (DSP_ADAU1452) */
#define REG_MP0_MODE_DSP_ADAU1452_ADDR            0xF510
#define REG_MP0_MODE_DSP_ADAU1452_BYTE            2
#define REG_MP0_MODE_DSP_ADAU1452_VALUE           0x5

/* MP1_MODE  - Registers (DSP_ADAU1452) */
#define REG_MP1_MODE_DSP_ADAU1452_ADDR            0xF511
#define REG_MP1_MODE_DSP_ADAU1452_BYTE            2
#define REG_MP1_MODE_DSP_ADAU1452_VALUE           0x0

/* MP2_MODE  - Registers (DSP_ADAU1452) */
#define REG_MP2_MODE_DSP_ADAU1452_ADDR            0xF512
#define REG_MP2_MODE_DSP_ADAU1452_BYTE            2
#define REG_MP2_MODE_DSP_ADAU1452_VALUE           0x0

/* MP3_MODE  - Registers (DSP_ADAU1452) */
#define REG_MP3_MODE_DSP_ADAU1452_ADDR            0xF513
#define REG_MP3_MODE_DSP_ADAU1452_BYTE            2
#define REG_MP3_MODE_DSP_ADAU1452_VALUE           0x0

/* MP4_MODE  - Registers (DSP_ADAU1452) */
#define REG_MP4_MODE_DSP_ADAU1452_ADDR            0xF514
#define REG_MP4_MODE_DSP_ADAU1452_BYTE            2
#define REG_MP4_MODE_DSP_ADAU1452_VALUE           0x0

/* MP5_MODE  - Registers (DSP_ADAU1452) */
#define REG_MP5_MODE_DSP_ADAU1452_ADDR            0xF515
#define REG_MP5_MODE_DSP_ADAU1452_BYTE            2
#define REG_MP5_MODE_DSP_ADAU1452_VALUE           0x0

/* MP6_MODE  - Registers (DSP_ADAU1452) */
#define REG_MP6_MODE_DSP_ADAU1452_ADDR            0xF516
#define REG_MP6_MODE_DSP_ADAU1452_BYTE            2
#define REG_MP6_MODE_DSP_ADAU1452_VALUE           0x0

/* MP7_MODE  - Registers (DSP_ADAU1452) */
#define REG_MP7_MODE_DSP_ADAU1452_ADDR            0xF517
#define REG_MP7_MODE_DSP_ADAU1452_BYTE            2
#define REG_MP7_MODE_DSP_ADAU1452_VALUE           0x0

/* MP8_MODE  - Registers (DSP_ADAU1452) */
#define REG_MP8_MODE_DSP_ADAU1452_ADDR            0xF518
#define REG_MP8_MODE_DSP_ADAU1452_BYTE            2
#define REG_MP8_MODE_DSP_ADAU1452_VALUE           0x0

/* MP9_MODE  - Registers (DSP_ADAU1452) */
#define REG_MP9_MODE_DSP_ADAU1452_ADDR            0xF519
#define REG_MP9_MODE_DSP_ADAU1452_BYTE            2
#define REG_MP9_MODE_DSP_ADAU1452_VALUE           0x0

/* MP10_MODE  - Registers (DSP_ADAU1452) */
#define REG_MP10_MODE_DSP_ADAU1452_ADDR           0xF51A
#define REG_MP10_MODE_DSP_ADAU1452_BYTE           2
#define REG_MP10_MODE_DSP_ADAU1452_VALUE          0x0

/* MP11_MODE  - Registers (DSP_ADAU1452) */
#define REG_MP11_MODE_DSP_ADAU1452_ADDR           0xF51B
#define REG_MP11_MODE_DSP_ADAU1452_BYTE           2
#define REG_MP11_MODE_DSP_ADAU1452_VALUE          0x0

/* MP12_MODE  - Registers (DSP_ADAU1452) */
#define REG_MP12_MODE_DSP_ADAU1452_ADDR           0xF51C
#define REG_MP12_MODE_DSP_ADAU1452_BYTE           2
#define REG_MP12_MODE_DSP_ADAU1452_VALUE          0x0

/* MP13_MODE  - Registers (DSP_ADAU1452) */
#define REG_MP13_MODE_DSP_ADAU1452_ADDR           0xF51D
#define REG_MP13_MODE_DSP_ADAU1452_BYTE           2
#define REG_MP13_MODE_DSP_ADAU1452_VALUE          0x0

/* MP0_WRITE  - Registers (DSP_ADAU1452) */
#define REG_MP0_WRITE_DSP_ADAU1452_ADDR           0xF520
#define REG_MP0_WRITE_DSP_ADAU1452_BYTE           2
#define REG_MP0_WRITE_DSP_ADAU1452_VALUE          0x0

/* MP1_WRITE  - Registers (DSP_ADAU1452) */
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
#define REG_MP6_READ_DSP_ADAU1452_VALUE           0x0

/* MP7_READ  - Registers (DSP_ADAU1452) */
#define REG_MP7_READ_DSP_ADAU1452_ADDR            0xF537
#define REG_MP7_READ_DSP_ADAU1452_BYTE            0
#define REG_MP7_READ_DSP_ADAU1452_VALUE           0x0

/* MP8_READ  - Registers (DSP_ADAU1452) */
#define REG_MP8_READ_DSP_ADAU1452_ADDR            0xF538
#define REG_MP8_READ_DSP_ADAU1452_BYTE            0
#define REG_MP8_READ_DSP_ADAU1452_VALUE           0x0

/* MP9_READ  - Registers (DSP_ADAU1452) */
#define REG_MP9_READ_DSP_ADAU1452_ADDR            0xF539
#define REG_MP9_READ_DSP_ADAU1452_BYTE            0
#define REG_MP9_READ_DSP_ADAU1452_VALUE           0x0

/* MP10_READ  - Registers (DSP_ADAU1452) */
#define REG_MP10_READ_DSP_ADAU1452_ADDR           0xF53A
#define REG_MP10_READ_DSP_ADAU1452_BYTE           0
#define REG_MP10_READ_DSP_ADAU1452_VALUE          0x0

/* MP11_READ  - Registers (DSP_ADAU1452) */
#define REG_MP11_READ_DSP_ADAU1452_ADDR           0xF53B
#define REG_MP11_READ_DSP_ADAU1452_BYTE           0
#define REG_MP11_READ_DSP_ADAU1452_VALUE          0x0

/* MP12_READ  - Registers (DSP_ADAU1452) */
#define REG_MP12_READ_DSP_ADAU1452_ADDR           0xF53C
#define REG_MP12_READ_DSP_ADAU1452_BYTE           0
#define REG_MP12_READ_DSP_ADAU1452_VALUE          0x0

/* MP13_READ  - Registers (DSP_ADAU1452) */
#define REG_MP13_READ_DSP_ADAU1452_ADDR           0xF53D
#define REG_MP13_READ_DSP_ADAU1452_BYTE           0
#define REG_MP13_READ_DSP_ADAU1452_VALUE          0x0

/* DMIC_CTRL0  - Registers (DSP_ADAU1452) */
#define REG_DMIC_CTRL0_DSP_ADAU1452_ADDR          0xF560
#define REG_DMIC_CTRL0_DSP_ADAU1452_BYTE          2
#define REG_DMIC_CTRL0_DSP_ADAU1452_VALUE         0x4000

/* DMIC_CTRL1  - Registers (DSP_ADAU1452) */
#define REG_DMIC_CTRL1_DSP_ADAU1452_ADDR          0xF561
#define REG_DMIC_CTRL1_DSP_ADAU1452_BYTE          2
#define REG_DMIC_CTRL1_DSP_ADAU1452_VALUE         0x4000

/* ASRC_LOCK  - Registers (DSP_ADAU1452) */
#define REG_ASRC_LOCK_DSP_ADAU1452_ADDR           0xF580
#define REG_ASRC_LOCK_DSP_ADAU1452_BYTE           0
#define REG_ASRC_LOCK_DSP_ADAU1452_VALUE          0x4B

/* ASRC_MUTE  - Registers (DSP_ADAU1452) */
#define REG_ASRC_MUTE_DSP_ADAU1452_ADDR           0xF581
#define REG_ASRC_MUTE_DSP_ADAU1452_BYTE           2
#define REG_ASRC_MUTE_DSP_ADAU1452_VALUE          0x0

/* ASRC0_RATIO  - Registers (DSP_ADAU1452) */
#define REG_ASRC0_RATIO_DSP_ADAU1452_ADDR         0xF582
#define REG_ASRC0_RATIO_DSP_ADAU1452_BYTE         0
#define REG_ASRC0_RATIO_DSP_ADAU1452_VALUE        0x2000

/* ASRC1_RATIO  - Registers (DSP_ADAU1452) */
#define REG_ASRC1_RATIO_DSP_ADAU1452_ADDR         0xF583
#define REG_ASRC1_RATIO_DSP_ADAU1452_BYTE         0
#define REG_ASRC1_RATIO_DSP_ADAU1452_VALUE        0x1000

/* ASRC2_RATIO  - Registers (DSP_ADAU1452) */
#define REG_ASRC2_RATIO_DSP_ADAU1452_ADDR         0xF584
#define REG_ASRC2_RATIO_DSP_ADAU1452_BYTE         0
#define REG_ASRC2_RATIO_DSP_ADAU1452_VALUE        0x0

/* ASRC3_RATIO  - Registers (DSP_ADAU1452) */
#define REG_ASRC3_RATIO_DSP_ADAU1452_ADDR         0xF585
#define REG_ASRC3_RATIO_DSP_ADAU1452_BYTE         0
#define REG_ASRC3_RATIO_DSP_ADAU1452_VALUE        0x1000

/* ASRC4_RATIO  - Registers (DSP_ADAU1452) */
#define REG_ASRC4_RATIO_DSP_ADAU1452_ADDR         0xF586
#define REG_ASRC4_RATIO_DSP_ADAU1452_BYTE         0
#define REG_ASRC4_RATIO_DSP_ADAU1452_VALUE        0x0

/* ASRC5_RATIO  - Registers (DSP_ADAU1452) */
#define REG_ASRC5_RATIO_DSP_ADAU1452_ADDR         0xF587
#define REG_ASRC5_RATIO_DSP_ADAU1452_BYTE         0
#define REG_ASRC5_RATIO_DSP_ADAU1452_VALUE        0x0

/* ASRC6_RATIO  - Registers (DSP_ADAU1452) */
#define REG_ASRC6_RATIO_DSP_ADAU1452_ADDR         0xF588
#define REG_ASRC6_RATIO_DSP_ADAU1452_BYTE         0
#define REG_ASRC6_RATIO_DSP_ADAU1452_VALUE        0x1000

/* ASRC7_RATIO  - Registers (DSP_ADAU1452) */
#define REG_ASRC7_RATIO_DSP_ADAU1452_ADDR         0xF589
#define REG_ASRC7_RATIO_DSP_ADAU1452_BYTE         0
#define REG_ASRC7_RATIO_DSP_ADAU1452_VALUE        0x0

/* ADC_READ0  - Registers (DSP_ADAU1452) */
#define REG_ADC_READ0_DSP_ADAU1452_ADDR           0xF5A0
#define REG_ADC_READ0_DSP_ADAU1452_BYTE           0
#define REG_ADC_READ0_DSP_ADAU1452_VALUE          0x1F

/* ADC_READ1  - Registers (DSP_ADAU1452) */
#define REG_ADC_READ1_DSP_ADAU1452_ADDR           0xF5A1
#define REG_ADC_READ1_DSP_ADAU1452_BYTE           0
#define REG_ADC_READ1_DSP_ADAU1452_VALUE          0x5C

/* ADC_READ2  - Registers (DSP_ADAU1452) */
#define REG_ADC_READ2_DSP_ADAU1452_ADDR           0xF5A2
#define REG_ADC_READ2_DSP_ADAU1452_BYTE           0
#define REG_ADC_READ2_DSP_ADAU1452_VALUE          0xB7

/* ADC_READ3  - Registers (DSP_ADAU1452) */
#define REG_ADC_READ3_DSP_ADAU1452_ADDR           0xF5A3
#define REG_ADC_READ3_DSP_ADAU1452_BYTE           0
#define REG_ADC_READ3_DSP_ADAU1452_VALUE          0xF1

/* ADC_READ4  - Registers (DSP_ADAU1452) */
#define REG_ADC_READ4_DSP_ADAU1452_ADDR           0xF5A4
#define REG_ADC_READ4_DSP_ADAU1452_BYTE           0
#define REG_ADC_READ4_DSP_ADAU1452_VALUE          0xAD

/* ADC_READ5  - Registers (DSP_ADAU1452) */
#define REG_ADC_READ5_DSP_ADAU1452_ADDR           0xF5A5
#define REG_ADC_READ5_DSP_ADAU1452_BYTE           0
#define REG_ADC_READ5_DSP_ADAU1452_VALUE          0x109

/* SPDIF_LOCK_DET  - Registers (DSP_ADAU1452) */
#define REG_SPDIF_LOCK_DET_DSP_ADAU1452_ADDR      0xF600
#define REG_SPDIF_LOCK_DET_DSP_ADAU1452_BYTE      0
#define REG_SPDIF_LOCK_DET_DSP_ADAU1452_VALUE     0x0

/* SPDIF_RX_CTRL  - Registers (DSP_ADAU1452) */
#define REG_SPDIF_RX_CTRL_DSP_ADAU1452_ADDR       0xF601
#define REG_SPDIF_RX_CTRL_DSP_ADAU1452_BYTE       2
#define REG_SPDIF_RX_CTRL_DSP_ADAU1452_VALUE      0x0

/* SPDIF_RX_DECODE  - Registers (DSP_ADAU1452) */
#define REG_SPDIF_RX_DECODE_DSP_ADAU1452_ADDR     0xF602
#define REG_SPDIF_RX_DECODE_DSP_ADAU1452_BYTE     0
#define REG_SPDIF_RX_DECODE_DSP_ADAU1452_VALUE    0x88

/* SPDIF_RX_COMPRMODE  - Registers (DSP_ADAU1452) */
#define REG_SPDIF_RX_COMPRMODE_DSP_ADAU1452_ADDR  0xF603
#define REG_SPDIF_RX_COMPRMODE_DSP_ADAU1452_BYTE  0
#define REG_SPDIF_RX_COMPRMODE_DSP_ADAU1452_VALUE 0x0

/* SPDIF_RESTART  - Registers (DSP_ADAU1452) */
#define REG_SPDIF_RESTART_DSP_ADAU1452_ADDR       0xF604
#define REG_SPDIF_RESTART_DSP_ADAU1452_BYTE       2
#define REG_SPDIF_RESTART_DSP_ADAU1452_VALUE      0x1

/* SPDIF_LOSS_OF_LOCK  - Registers (DSP_ADAU1452) */
#define REG_SPDIF_LOSS_OF_LOCK_DSP_ADAU1452_ADDR  0xF605
#define REG_SPDIF_LOSS_OF_LOCK_DSP_ADAU1452_BYTE  0
#define REG_SPDIF_LOSS_OF_LOCK_DSP_ADAU1452_VALUE 0x0

/* SPDIF_AUX_EN  - Registers (DSP_ADAU1452) */
#define REG_SPDIF_AUX_EN_DSP_ADAU1452_ADDR        0xF608
#define REG_SPDIF_AUX_EN_DSP_ADAU1452_BYTE        2
#define REG_SPDIF_AUX_EN_DSP_ADAU1452_VALUE       0x0

/* SPDIF_RX_AUXBIT_READY  - Registers (DSP_ADAU1452) */
#define REG_SPDIF_RX_AUXBIT_READY_DSP_ADAU1452_ADDR 0xF60F
#define REG_SPDIF_RX_AUXBIT_READY_DSP_ADAU1452_BYTE 0
#define REG_SPDIF_RX_AUXBIT_READY_DSP_ADAU1452_VALUE 0x0

/* SPDIF_RX_CS_LEFT_0  - Registers (DSP_ADAU1452) */
#define REG_SPDIF_RX_CS_LEFT_0_DSP_ADAU1452_ADDR  0xF610
#define REG_SPDIF_RX_CS_LEFT_0_DSP_ADAU1452_BYTE  0
#define REG_SPDIF_RX_CS_LEFT_0_DSP_ADAU1452_VALUE 0x0

/* SPDIF_RX_CS_LEFT_1  - Registers (DSP_ADAU1452) */
#define REG_SPDIF_RX_CS_LEFT_1_DSP_ADAU1452_ADDR  0xF611
#define REG_SPDIF_RX_CS_LEFT_1_DSP_ADAU1452_BYTE  0
#define REG_SPDIF_RX_CS_LEFT_1_DSP_ADAU1452_VALUE 0x0

/* SPDIF_RX_CS_LEFT_2  - Registers (DSP_ADAU1452) */
#define REG_SPDIF_RX_CS_LEFT_2_DSP_ADAU1452_ADDR  0xF612
#define REG_SPDIF_RX_CS_LEFT_2_DSP_ADAU1452_BYTE  0
#define REG_SPDIF_RX_CS_LEFT_2_DSP_ADAU1452_VALUE 0x0

/* SPDIF_RX_CS_LEFT_3  - Registers (DSP_ADAU1452) */
#define REG_SPDIF_RX_CS_LEFT_3_DSP_ADAU1452_ADDR  0xF613
#define REG_SPDIF_RX_CS_LEFT_3_DSP_ADAU1452_BYTE  0
#define REG_SPDIF_RX_CS_LEFT_3_DSP_ADAU1452_VALUE 0x0

/* SPDIF_RX_CS_LEFT_4  - Registers (DSP_ADAU1452) */
#define REG_SPDIF_RX_CS_LEFT_4_DSP_ADAU1452_ADDR  0xF614
#define REG_SPDIF_RX_CS_LEFT_4_DSP_ADAU1452_BYTE  0
#define REG_SPDIF_RX_CS_LEFT_4_DSP_ADAU1452_VALUE 0x0

/* SPDIF_RX_CS_LEFT_5  - Registers (DSP_ADAU1452) */
#define REG_SPDIF_RX_CS_LEFT_5_DSP_ADAU1452_ADDR  0xF615
#define REG_SPDIF_RX_CS_LEFT_5_DSP_ADAU1452_BYTE  0
#define REG_SPDIF_RX_CS_LEFT_5_DSP_ADAU1452_VALUE 0x0

/* SPDIF_RX_CS_LEFT_6  - Registers (DSP_ADAU1452) */
#define REG_SPDIF_RX_CS_LEFT_6_DSP_ADAU1452_ADDR  0xF616
#define REG_SPDIF_RX_CS_LEFT_6_DSP_ADAU1452_BYTE  0
#define REG_SPDIF_RX_CS_LEFT_6_DSP_ADAU1452_VALUE 0x0

/* SPDIF_RX_CS_LEFT_7  - Registers (DSP_ADAU1452) */
#define REG_SPDIF_RX_CS_LEFT_7_DSP_ADAU1452_ADDR  0xF617
#define REG_SPDIF_RX_CS_LEFT_7_DSP_ADAU1452_BYTE  0
#define REG_SPDIF_RX_CS_LEFT_7_DSP_ADAU1452_VALUE 0x0

/* SPDIF_RX_CS_LEFT_8  - Registers (DSP_ADAU1452) */
#define REG_SPDIF_RX_CS_LEFT_8_DSP_ADAU1452_ADDR  0xF618
#define REG_SPDIF_RX_CS_LEFT_8_DSP_ADAU1452_BYTE  0
#define REG_SPDIF_RX_CS_LEFT_8_DSP_ADAU1452_VALUE 0x0

/* SPDIF_RX_CS_LEFT_9  - Registers (DSP_ADAU1452) */
#define REG_SPDIF_RX_CS_LEFT_9_DSP_ADAU1452_ADDR  0xF619
#define REG_SPDIF_RX_CS_LEFT_9_DSP_ADAU1452_BYTE  0
#define REG_SPDIF_RX_CS_LEFT_9_DSP_ADAU1452_VALUE 0x0

/* SPDIF_RX_CS_LEFT_10  - Registers (DSP_ADAU1452) */
#define REG_SPDIF_RX_CS_LEFT_10_DSP_ADAU1452_ADDR 0xF61A
#define REG_SPDIF_RX_CS_LEFT_10_DSP_ADAU1452_BYTE 0
#define REG_SPDIF_RX_CS_LEFT_10_DSP_ADAU1452_VALUE 0x0

/* SPDIF_RX_CS_LEFT_11  - Registers (DSP_ADAU1452) */
#define REG_SPDIF_RX_CS_LEFT_11_DSP_ADAU1452_ADDR 0xF61B
#define REG_SPDIF_RX_CS_LEFT_11_DSP_ADAU1452_BYTE 0
#define REG_SPDIF_RX_CS_LEFT_11_DSP_ADAU1452_VALUE 0x0

/* SPDIF_RX_CS_RIGHT_0  - Registers (DSP_ADAU1452) */
#define REG_SPDIF_RX_CS_RIGHT_0_DSP_ADAU1452_ADDR 0xF620
#define REG_SPDIF_RX_CS_RIGHT_0_DSP_ADAU1452_BYTE 0
#define REG_SPDIF_RX_CS_RIGHT_0_DSP_ADAU1452_VALUE 0x0

/* SPDIF_RX_CS_RIGHT_1  - Registers (DSP_ADAU1452) */
#define REG_SPDIF_RX_CS_RIGHT_1_DSP_ADAU1452_ADDR 0xF621
#define REG_SPDIF_RX_CS_RIGHT_1_DSP_ADAU1452_BYTE 0
#define REG_SPDIF_RX_CS_RIGHT_1_DSP_ADAU1452_VALUE 0x0

/* SPDIF_RX_CS_RIGHT_2  - Registers (DSP_ADAU1452) */
#define REG_SPDIF_RX_CS_RIGHT_2_DSP_ADAU1452_ADDR 0xF622
#define REG_SPDIF_RX_CS_RIGHT_2_DSP_ADAU1452_BYTE 0
#define REG_SPDIF_RX_CS_RIGHT_2_DSP_ADAU1452_VALUE 0x0

/* SPDIF_RX_CS_RIGHT_3  - Registers (DSP_ADAU1452) */
#define REG_SPDIF_RX_CS_RIGHT_3_DSP_ADAU1452_ADDR 0xF623
#define REG_SPDIF_RX_CS_RIGHT_3_DSP_ADAU1452_BYTE 0
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
#define REG_SPDIF_RX_PB_LEFT_0_DSP_ADAU1452_VALUE 0x0

/* SPDIF_RX_PB_LEFT_1  - Registers (DSP_ADAU1452) */
#define REG_SPDIF_RX_PB_LEFT_1_DSP_ADAU1452_ADDR  0xF671
#define REG_SPDIF_RX_PB_LEFT_1_DSP_ADAU1452_BYTE  0
#define REG_SPDIF_RX_PB_LEFT_1_DSP_ADAU1452_VALUE 0x0

/* SPDIF_RX_PB_LEFT_2  - Registers (DSP_ADAU1452) */
#define REG_SPDIF_RX_PB_LEFT_2_DSP_ADAU1452_ADDR  0xF672
#define REG_SPDIF_RX_PB_LEFT_2_DSP_ADAU1452_BYTE  0
#define REG_SPDIF_RX_PB_LEFT_2_DSP_ADAU1452_VALUE 0x0
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
